MikhailBerezhanov/MAMboard/docs/Radiator_ABM-161-30_HS-117-30.pdf

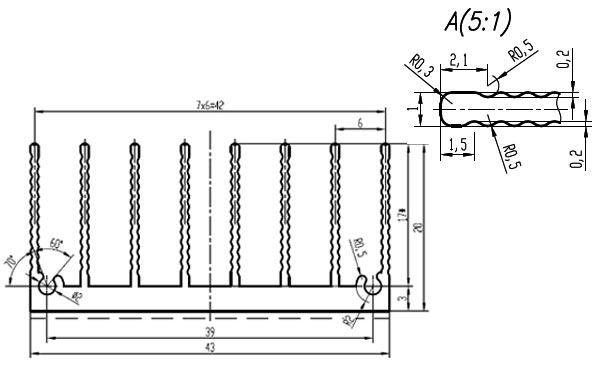
[picture p3: page 1]
