MikhailBerezhanov/MAMboard/docs/Battery_charger_TP4056_with_batt_protection_scheme.jpg

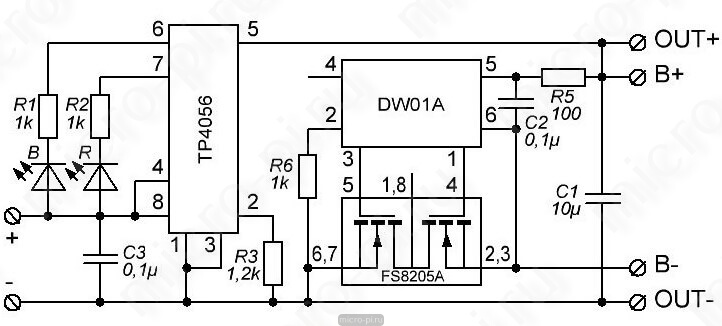
docs/Battery_charger_TP4056_with_batt_protection_scheme.jpg
