MikhailBerezhanov/MAMboard/docs/kak-podkluchit-regulator-gromkosti-k-usilitelu-resistor.jpg

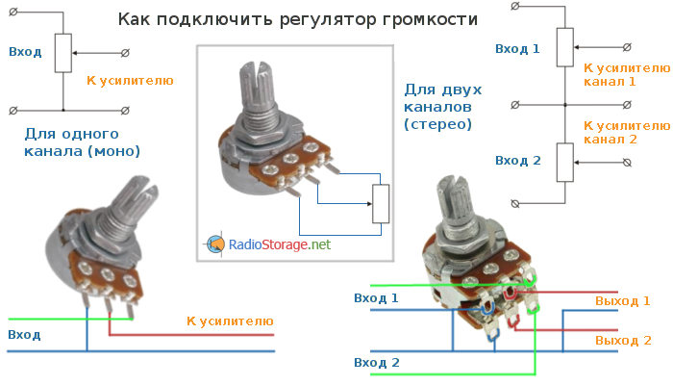
docs/kak-podkluchit-regulator-gromkosti-k-usilitelu-resistor.jpg
