MikhailBerezhanov/MAMboard/docs/LCD_I2C-PCF8574T-HAT.jpg

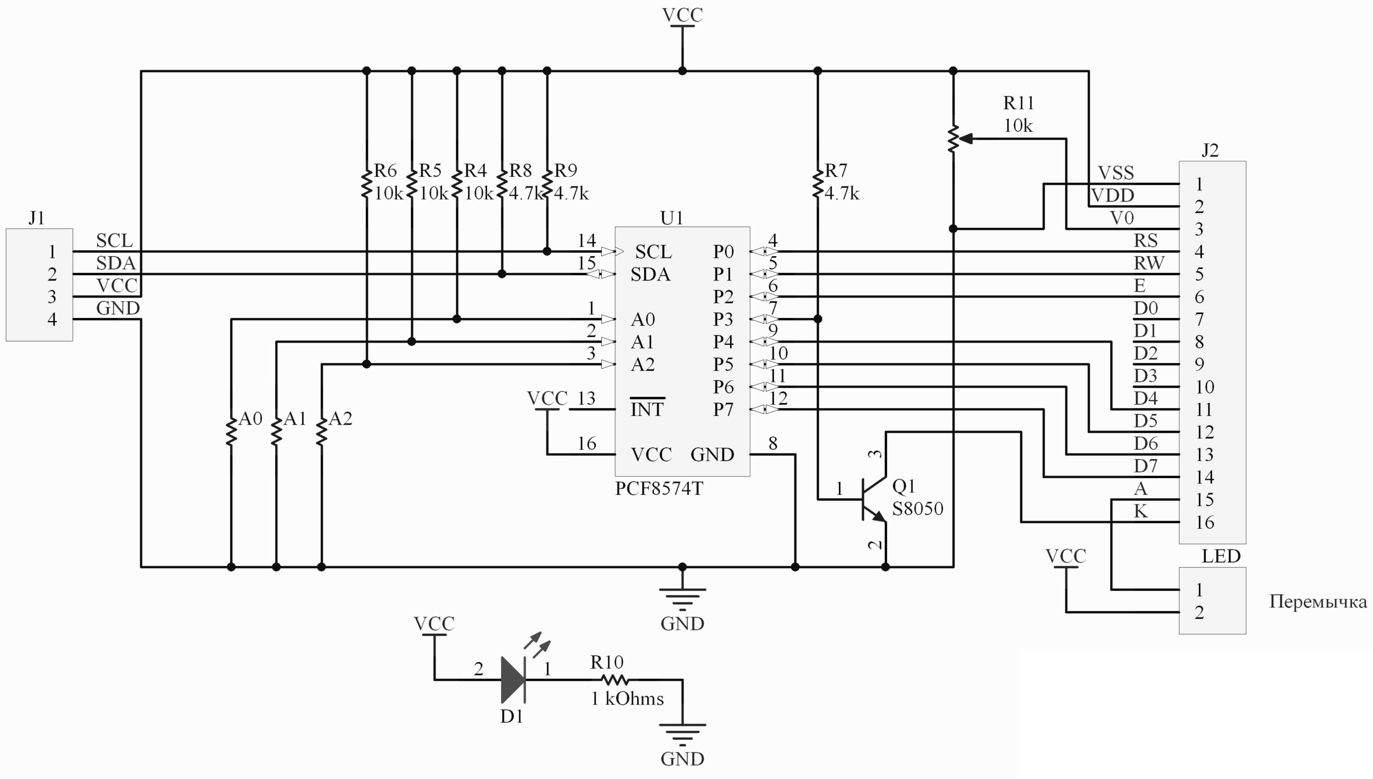
docs/LCD_I2C-PCF8574T-HAT.jpg
