MikhailBerezhanov/MAMboard/docs/midland_MA-26L.png

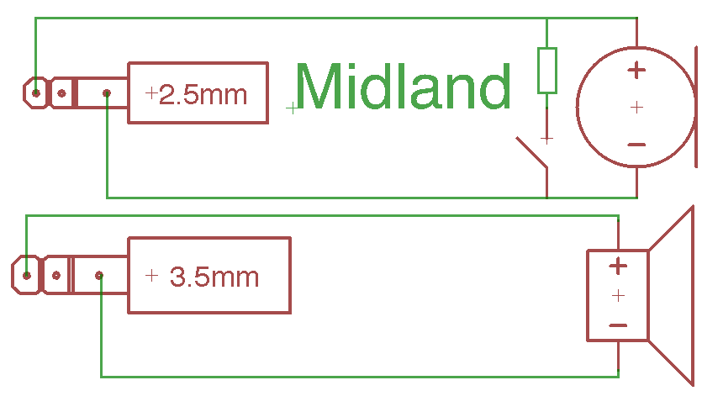
docs/midland_MA-26L.png
