MikhailBerezhanov/MAMboard/docs/NAU.jpg

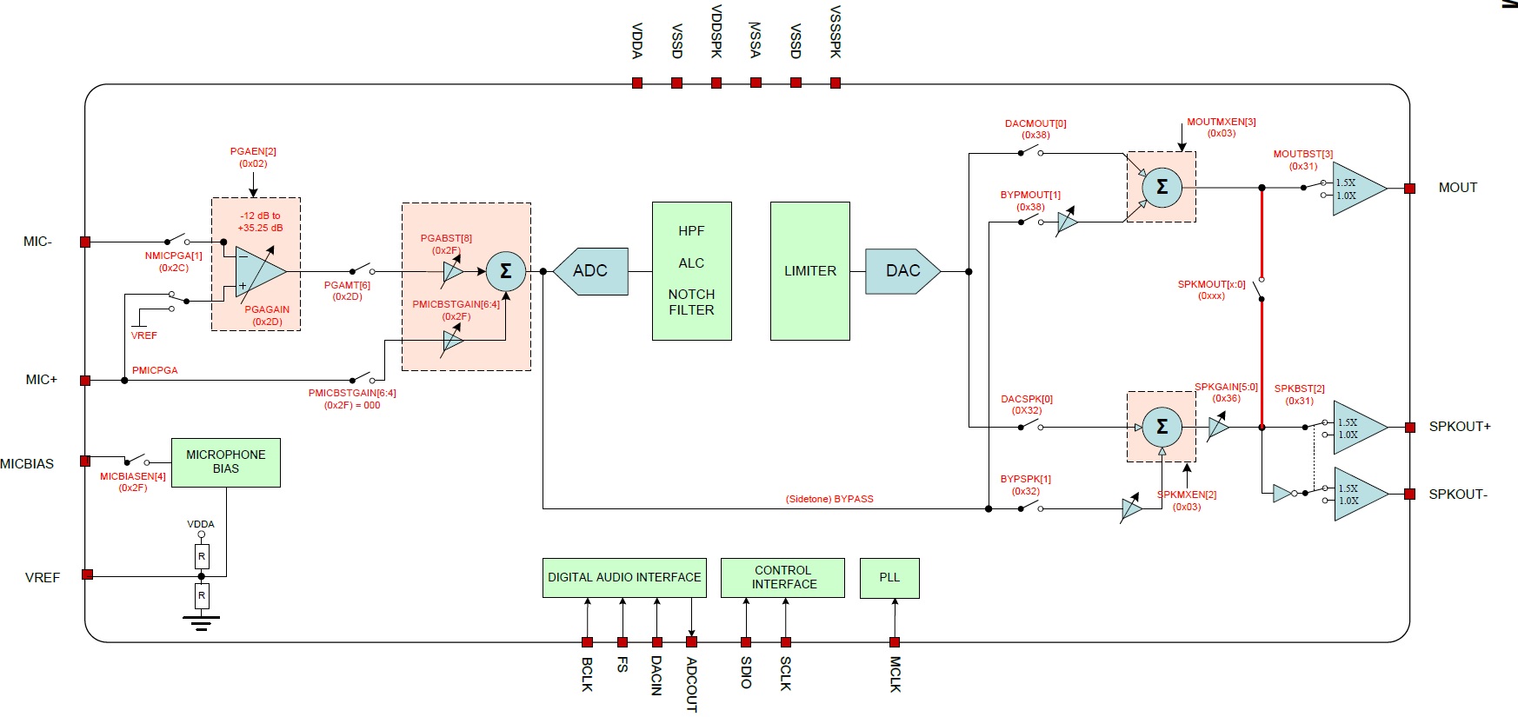
docs/NAU.jpg
