MikhailBerezhanov/MAMboard/docs/NAU_registers.jpg

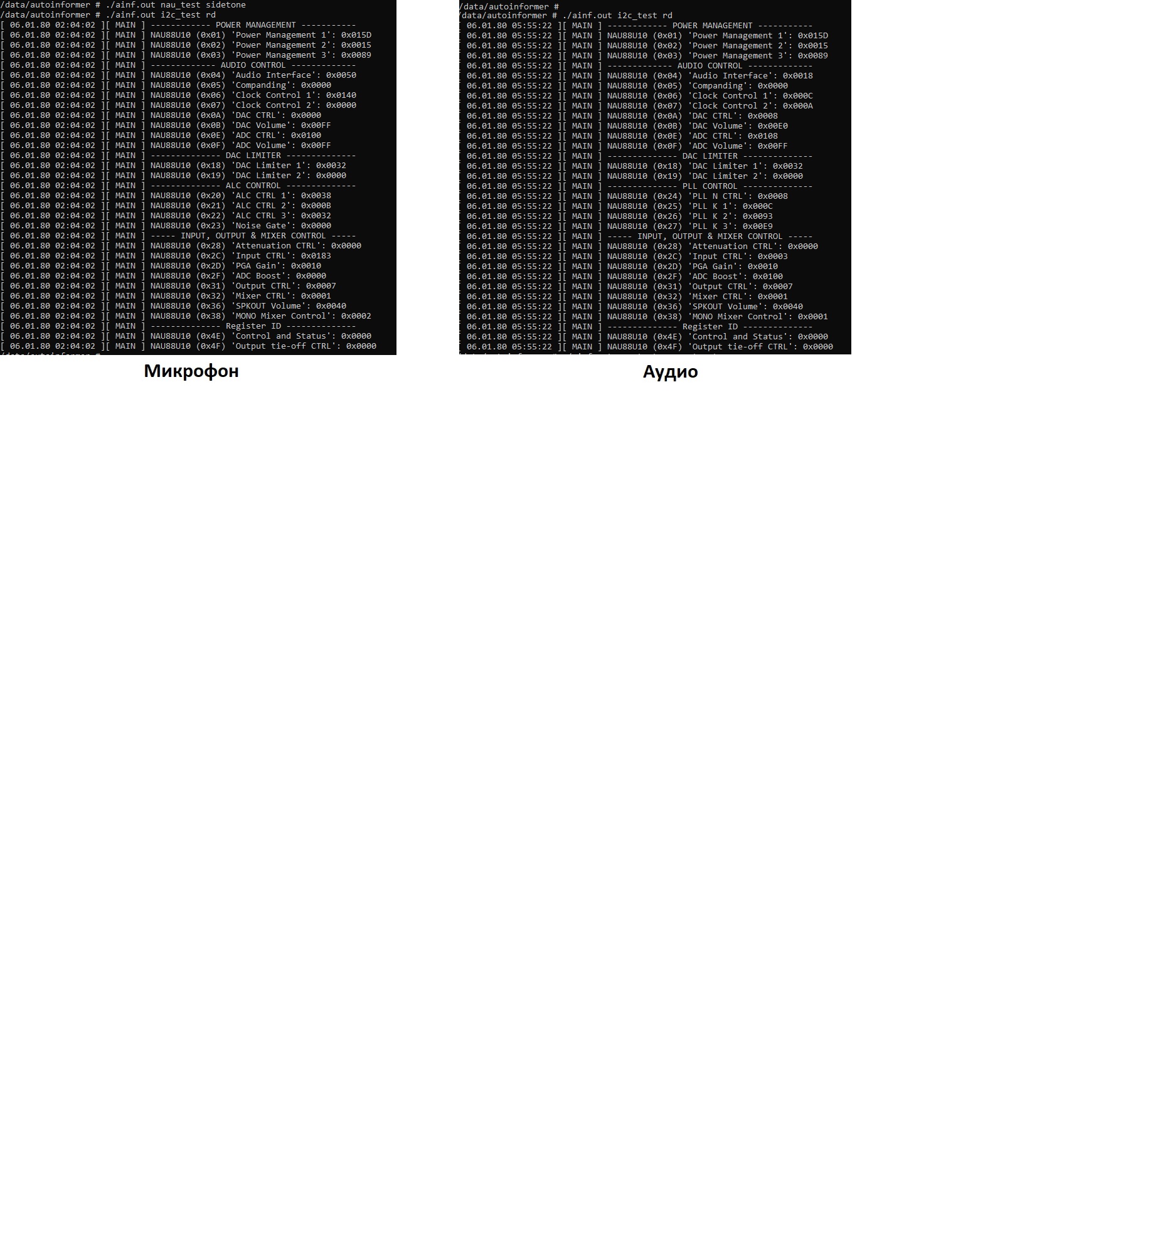
docs/NAU_registers.jpg
