MikhailBerezhanov/MAMboard/docs/oscilloscopes/LCD/PCA9306_I2C_with_10k_pullups.jpg

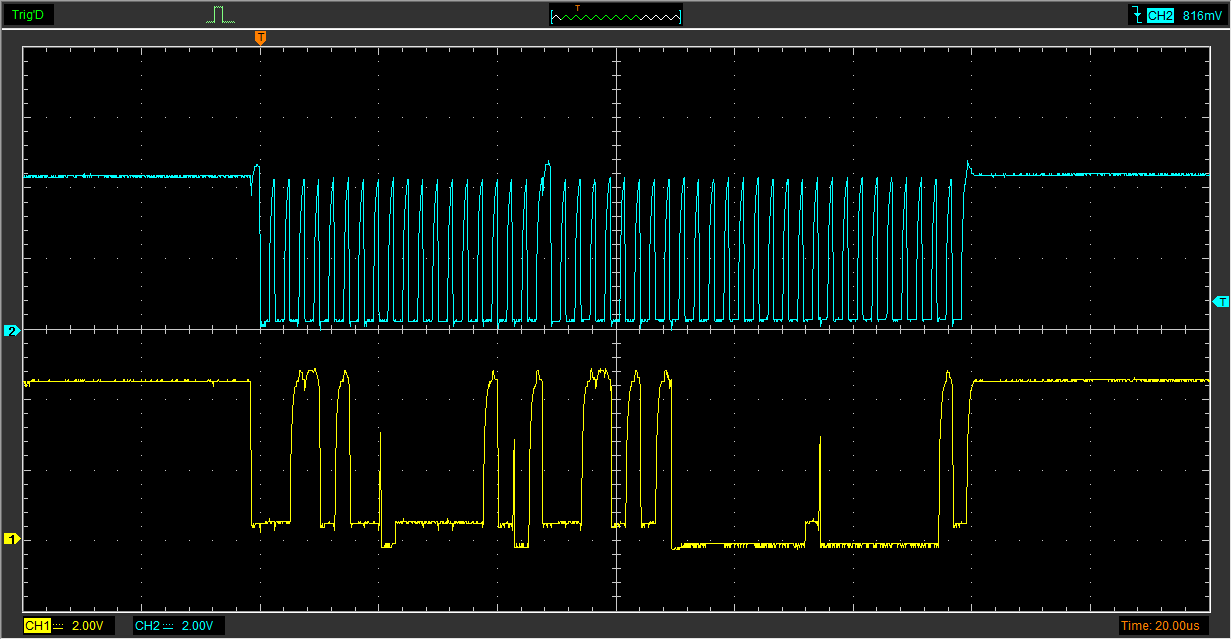
docs/oscilloscopes/LCD/PCA9306_I2C_with_10k_pullups.jpg
