MikhailBerezhanov/MAMboard/docs/oscilloscopes/LCD/stm32_100khz_7E.bmp

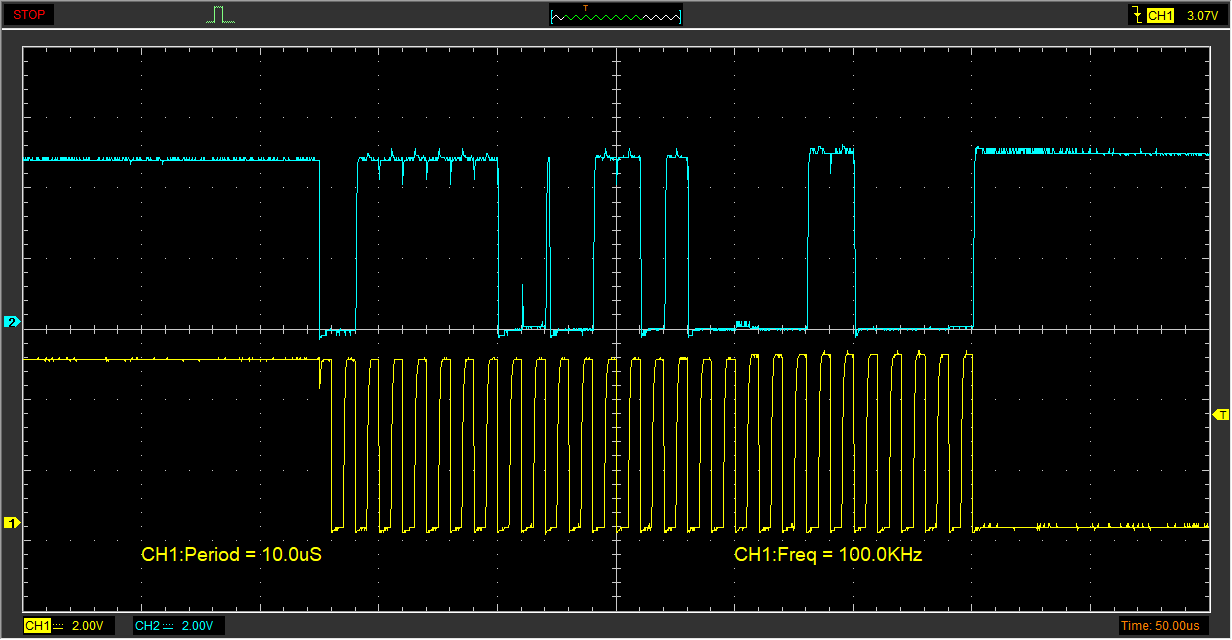
docs/oscilloscopes/LCD/stm32_100khz_7E.bmp
