MikhailBerezhanov/MAMboard/docs/oscilloscopes/NAU8810/PCM_CLK.jpg

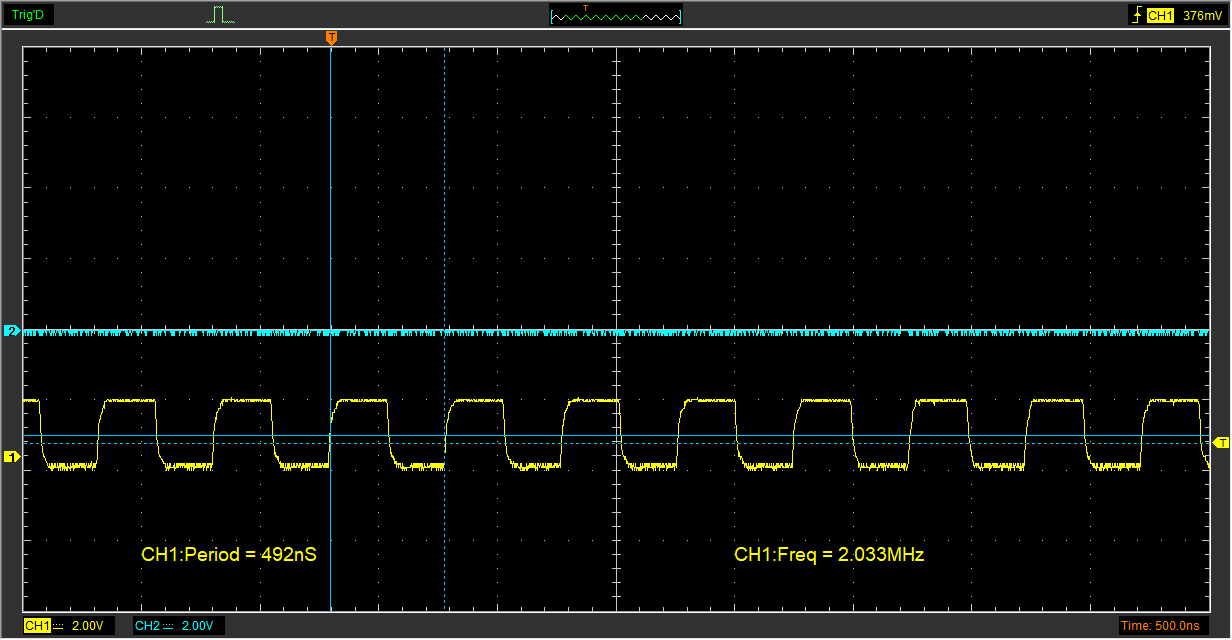
docs/oscilloscopes/NAU8810/PCM_CLK.jpg
