MikhailBerezhanov/MAMboard/docs/oscilloscopes/NAU8810/PCM_CLK_0.jpg

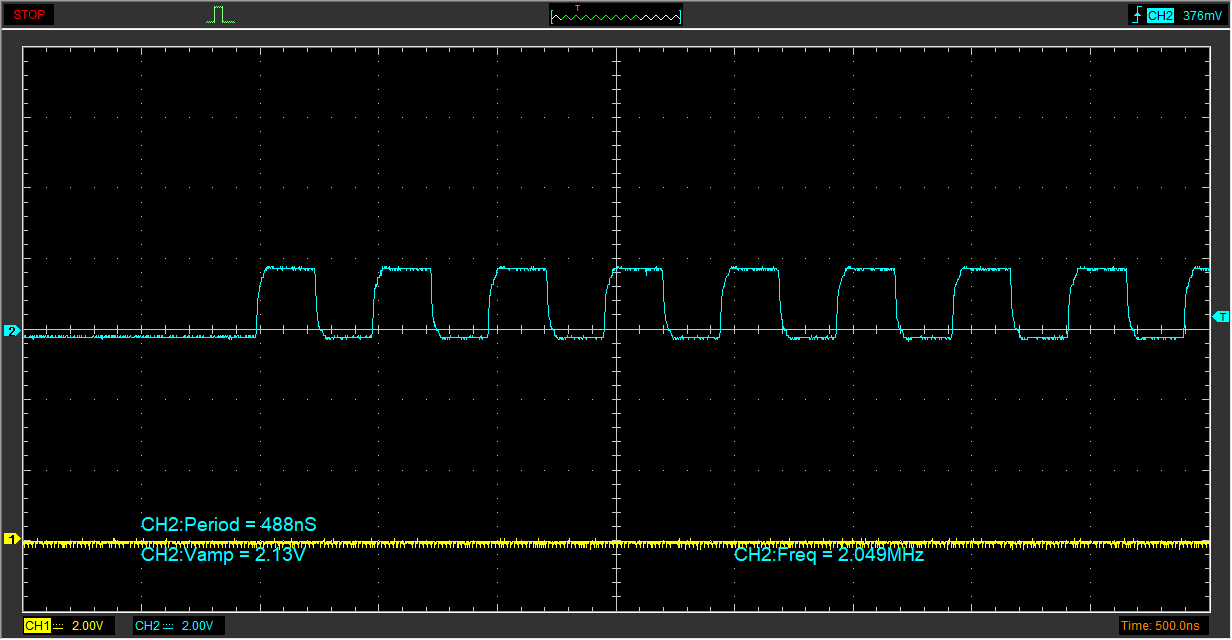
docs/oscilloscopes/NAU8810/PCM_CLK_0.jpg
