MikhailBerezhanov/MAMboard/docs/pcf_i2c_address.jpg

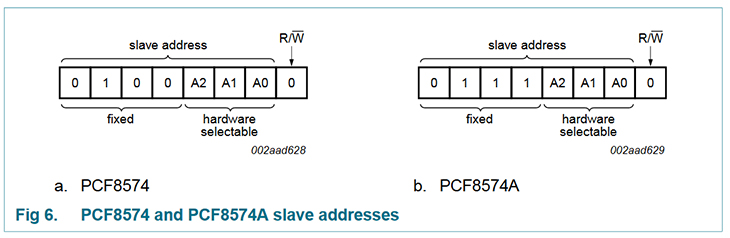
docs/pcf_i2c_address.jpg
