MikhailBerezhanov/MAMboard/docs/photo_2021-02-10_12-08-06.jpg

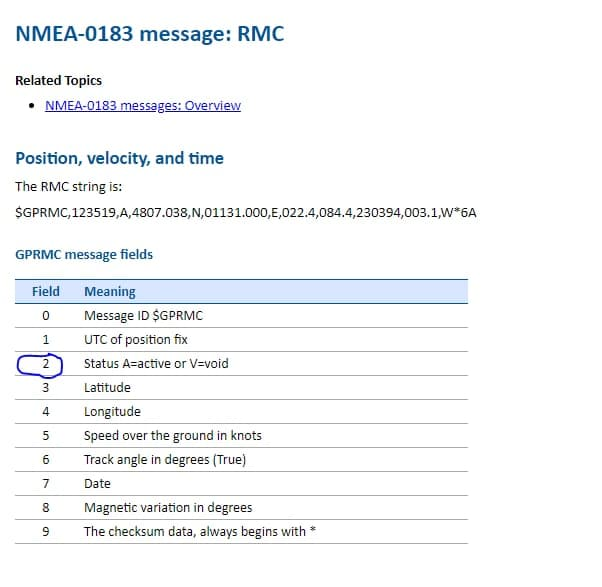
docs/photo_2021-02-10_12-08-06.jpg
