MikhailBerezhanov/MAMboard/docs/PJ-311D_connector.jpg

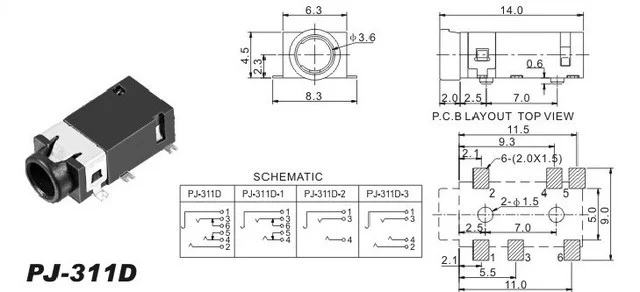
docs/PJ-311D_connector.jpg
