MikhailBerezhanov/MAMboard/docs/SIM7600-HEAD-CONNECTORS.jpg

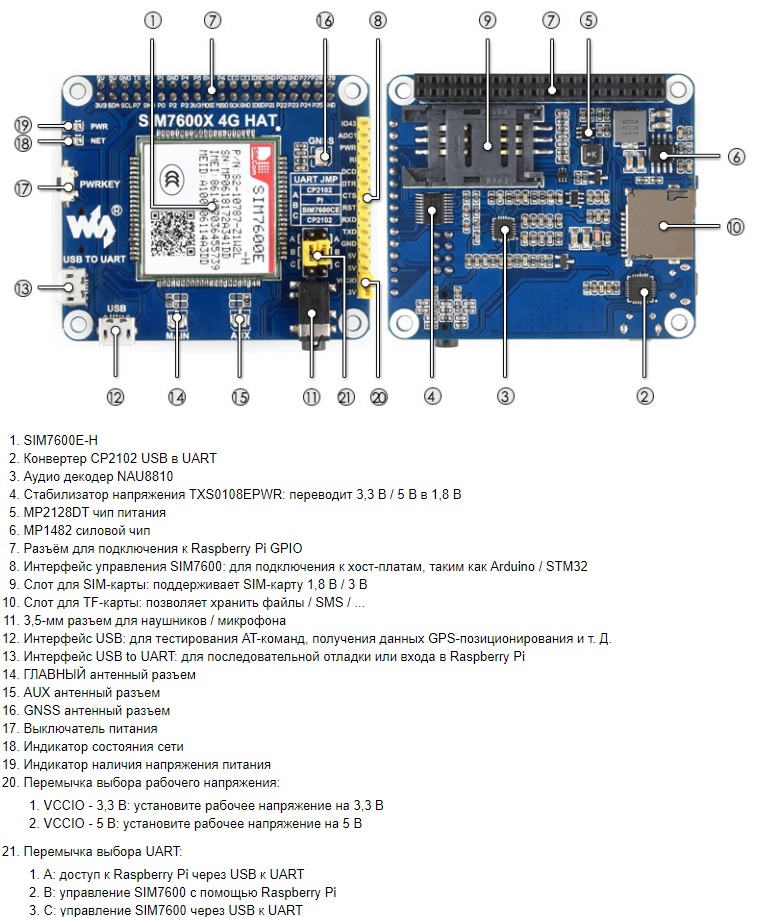
docs/SIM7600-HEAD-CONNECTORS.jpg
