MikhailBerezhanov/MAMboard/docs/usilitel-na-tda-2003-s-regulyatorom-gromkosti-2.gif

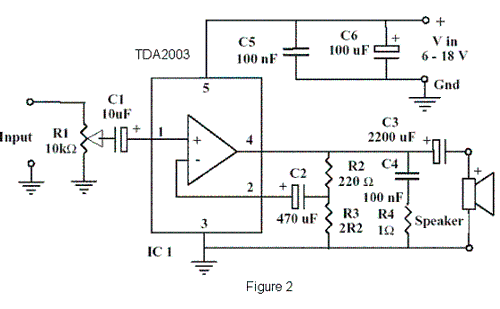
docs/usilitel-na-tda-2003-s-regulyatorom-gromkosti-2.gif
