MikhailBerezhanov/MAMboard/pcb/v1.1/GPIOs.jpg

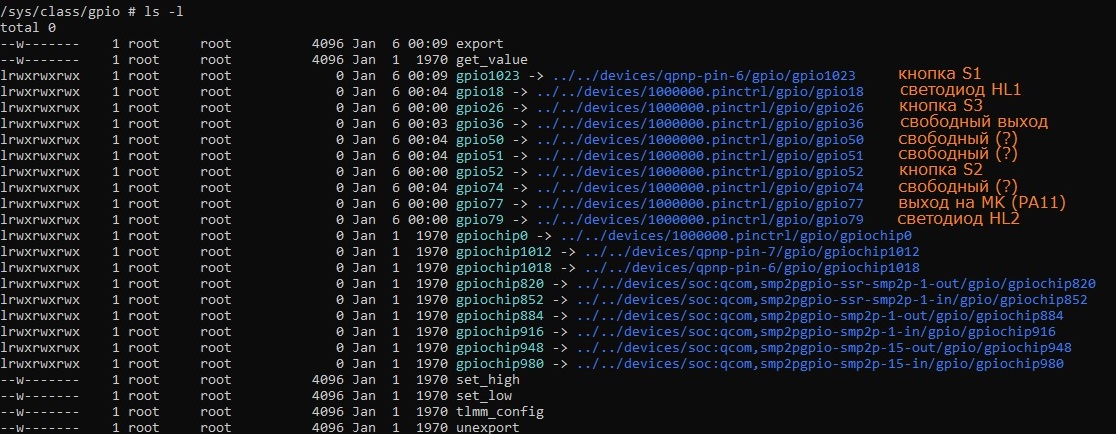
pcb/v1.1/GPIOs.jpg
