MikhailBerezhanov/MAMboard/pcb/v1.1/LCD_connector.jpg

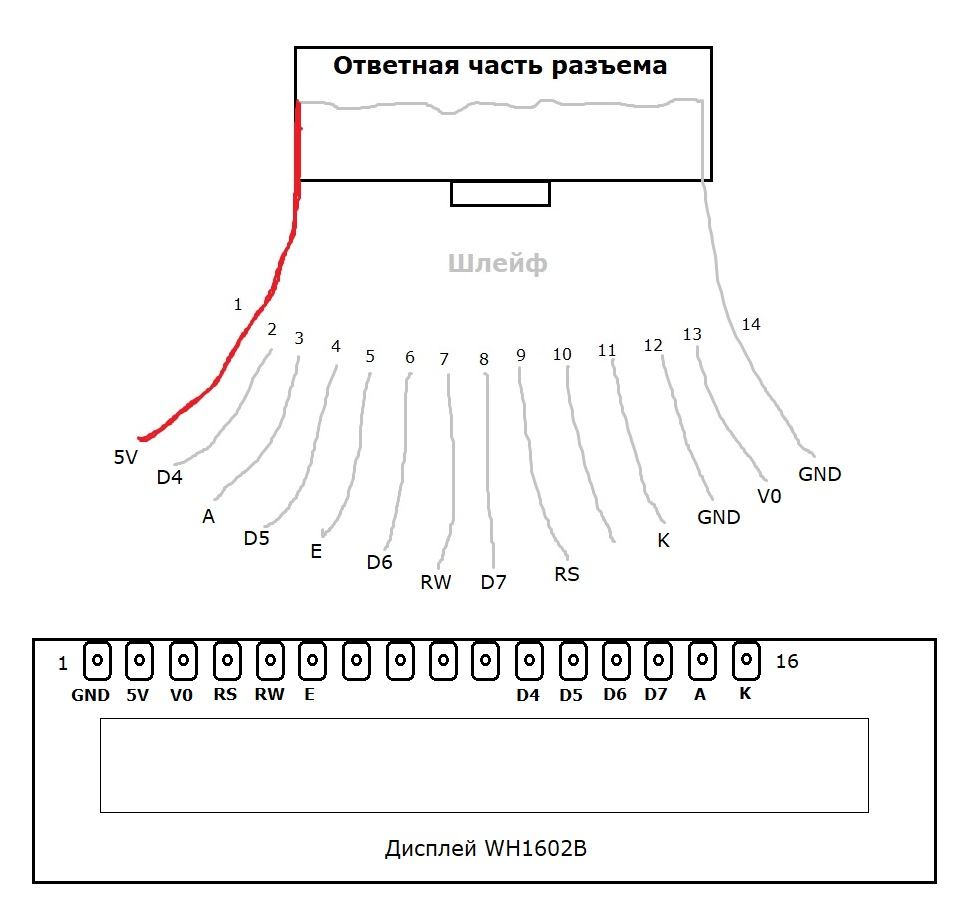
pcb/v1.1/LCD_connector.jpg
