MikhailBerezhanov/MAMboard/pcb/v1.1/Project Outputs for Autoinformer_v1.1/Autoinformer_v1.2pre_BOM.xls

Sheet: Autoinformer_v1.1
Конфигурация
 | Версия | Количество
 | v1.2pre | 15
Designator | Comment | Description | Quantity | Total | Link1URL | Link2URL | Link3URL | Link4URL | Link5URL | Link6URL | Link7URL
ANT1 | 146200-00011 | LTE Cellular Ceramic Antenna 698MHz-2.7GHz , SMT | 1 | 15 | https://www.elitan.ru/price/item17428368
C1, C11, C12, C13, C24, C28 | 4.7uF | GRM188R60J475KE19D | 6 | 90 | https://www.chipdip.ru/product/grm188r60j475ke19d | https://www.electronshik.ru/item/MUR/GRM188R60J475KE19D
C2, C3, C8, C14, C15, C16, C32, C34, C35, C40, C45, C46, C47, C48, C49, C52, C53, C54, C59, C61, C67, C68, C71, C76, C77, C79, C82 | 0.1uF | GRM188R71H104KA93D | 27 | 405 | https://www.chipdip.ru/product0/226236018 | https://www.electronshik.ru/item/MUR/GRM188R71H104KA93D |  |  | плюс 400
C4, C6, C17, C18, C29 | 10pF | GRM1885C1H100J | 5 | 75 | https://www.chipdip.ru/product/grm1885c1h100j | https://www.electronshik.ru/item/MUR/GRM1885C1H100JA01D
C5, C7, C9, C50, C51 | 22pF | GRM1885C1H220JA01D | 5 | 75 | https://www.chipdip.ru/product/grm1885c1h220j | https://www.electronshik.ru/item/MUR/GRM1885C1H220JA01D
C10 | 10nF | GRM188R71H103K | 1 | 15 | https://www.chipdip.ru/product0/9000143994 | https://www.electronshik.ru/item/MUR/GRM188R71H103KA01D
C19, C20, C44 | 33pF | GRM1885C1H330J | 3 | 45 | https://www.chipdip.ru/product0/565764982 | https://www.electronshik.ru/item/MUR/GRM1885C1H330JA01D
C21 | 100pF | GRM1885C1H101J | 1 | 15 | https://www.chipdip.ru/product0/305749128 | https://www.electronshik.ru/item/MUR/GRM1885C1H101JA01D
C22, C23, C25, C63 | 1uF | GRM188R71E105KA12D | 4 | 60 | https://www.chipdip.ru/product/grm188r71e105ka12d | https://www.electronshik.ru/item/MUR/GRM188R71E105KA12D
C26, C27 | 470uF 6.3V | 293D477X06R3E2TE3 Конденсатор танталовый SMD тип Е | 2 | 30 | https://www.chipdip.ru/product0/145634327?from=suggest_product
C30 | 1uF | GRM31MR71E105KA01L | 1 | 15 | https://www.chipdip.ru/product/grm31mr71e105k | https://www.electronshik.ru/item/MUR/GRM31MR71E105KA01L
C31 | 10uF 10V | Конденсатор танталовый SMD 10uF 10V тип B | 1 | 15 | https://www.chipdip.ru/product0/146061461?from=suggest_product
C33, C80, C81 | 0.1uF | CL05B104KO5NNNC (CC0402KRX7R7BB104) | 3 | 45 | https://www.chipdip.ru/product1/8001849671?from=suggest_product | https://www.electronshik.ru/item/SAMSUNG/CL05B104KO5NNNC
C36 | 0.039uF | CC0603KRX7R9BB393 | 1 | 15 | https://www.chipdip.ru/product0/8160066189?from=suggest_product | https://www.elitan.ru/price/item8778633 | https://www.electronshik.ru/item/YAG/CC0603KRX7R9BB393
C37 | K50-35 470uF 16V | Конденсатор электролитический алюминиевый 470мкФ, 16В, 8х12мм Р:3.5мм | 1 | 15 | https://www.chipdip.ru/product0/9000565914
C38, C39 | K50-35 1000uF 25V | Конденсатор электролитический алюминиевый 1000мкФ, 25В, 10x21мм | 2 | 30 | https://www.chipdip.ru/product0/9000565765?from=suggest_product
C41 | 22pF | GRM21A5C2E220J (CC0805JRNPO9BN220) | 1 | 15 | https://www.chipdip.ru/product0/29844 | https://www.electronshik.ru/item/MUR/GRM21A5C2E220JW01D
C42, C43 | NС | 0603 SMD Capacitor | 2 | 30
C55 | 100pF 2kV | C1206C101KGRACAUTO (CC1206JKNPODBN101) | 1 | 15 | https://www.elitan.ru/price/item16896874 | https://www.electronshik.ru/item/KEM/C1206C101KGRACAUTO
C56 | K50-35 220uF 50V | SH050M0220B5S-1012 ECAP 10*12 Конденсатор электролитический алюминиевый | 1 | 15 | https://www.chipdip.ru/product0/9000565903
C57, C64 | 10uF | GRM188R61E106M | 2 | 30 | https://www.chipdip.ru/product/grm188r61e106m | https://www.electronshik.ru/item/MUR/GRM188R61E106MA73D
C58 | K50-35 220uF 16V | ECA1CM221 6.3x11 P:2,5мм Конденсатор электролитический алюминиевый | 1 | 15 | https://www.chipdip.ru/product0/9000565899
C60, C69, C74, C75 |  | ECA0JHG221 5x11мм Р:2,5мм Конденсатор электролитический алюминиевый | 4 | 60 | https://www.chipdip.ru/product0/9000261774?from=suggest_product
C62 | K50-35 100uF 16V | SH016M0100A2F-0511 5x11мм Конденсатор электролитический алюминиевый | 1 | 15 | https://www.chipdip.ru/product0/9000565888
C65, C78 | K50-35 33uF 6.3V | Конденсатор электролитический алюминиевый 33 мкФ, 6.3 В, 4х7мм | 2 | 30 | https://www.chipdip.ru/product0/9000261769
C66 | 0.47uF | C1608X7R1H474K080AC (CC0603KRX7R9BB474) | 1 | 15 | https://www.chipdip.ru/product0/8576565346 | https://www.electronshik.ru/item/TDK/C1608X7R1H474K080AC
C70 | K50-35 680uF 25V | Конденсатор электролитический алюминиевый 680мкФ, 25В, 10х16мм Р:5мм | 1 | 15 | https://www.chipdip.ru/product0/9000565919
C72, C73 | K50-35 100uF 10V | SH010M0100B2F-0511 5x11мм Конденсатор электролитический алюминиевый | 2 | 30 | https://www.chipdip.ru/product0/46079?from=suggest_product | https://www.chipdip.ru/product0/9000565886
D1 | SIM7600E-H | Multi-Band LTE-TDD/LTE-FDD/HSPA+ and GSM/GPRS/EDGE module | 1 | 15 | http://www.mt-system.ru/SIMCom/SIM7600E-H |  |  |  | плюс 1
D2 | NAU8810YG | AUDIO CODEC MONO 20QFN | 1 | 15 | https://upverter.com/upn/revision/eec1ccdac07fe113/ | http://www.nuvoton.com/hq/resource-download.jsp?tp_GUID=DA00-NAU8810.1 | https://www.elitan.ru/price/index.php?find=NAU8810YG&delay=-1&mfg=all&seenform=y
D3 | TXB0102DCU | Voltage Level Translator Bidirectional 1 Circuit 2 Channel 100Mbps 8-VSSOP | 1 | 15 | https://www.elitan.ru/price/item692394 | https://www.chipdip.ru/product0/8002872138?from=suggest_product | https://www.electronshik.ru/item/TI/TXB0102DCUR
D4 | TXB0104PWR | 4-Bit Bidirectional Voltage-Level Shifter with Auto Direction Sensing and +/-15 kV ESD Protect 14-TSSOP -40 to 85 | 1 | 15 | https://www.elitan.ru/price/item703962
D5 | DW01A | НЕ УСТАНАВЛИВАТЬ | 1 | 15
D6 | MCP130T-450I/TT | 4.50 V 150 ms Microcontroller Supervisory Circuit - SOT-23-3 | 1 | 15 | https://www.elitan.ru/price/item505438 | https://www.electronshik.ru/item/MCRCH/MCP130T-450I%3A%3ATT
D7 | NB3N501DG | PLL Clock Multiplier Single 8-Pin SOIC 3 V ~ 5.25 V | 1 | 15 | https://www.elitan.ru/price/item9787428 | https://www.electronshik.ru/item/ONS/NB3N501DG
D8 | PCF8574AT | 8-bit I/O expander for I2C bus with interrupt PCF8574(A)T/3 - 100kHz version PCA8574(A)D - 400kHz version | 1 | 15 | https://www.elitan.ru/price/item981552 | https://www.electronshik.ru/item/NXP/PCF8574AT%3A%3A3.518
DA1 | TDA2003V | Amplifier IC 1-Channel _Mono_ Class AB 5-PENTAWATT 10W | 1 | 15 | https://www.elitan.ru/price/item123031 | https://www.chipdip.ru/product/tda2003v?from=suggest_product | https://www.chipdip.ru/product/hs-117-30
DA2 | LM2576S-5.0 | Импульсный понижающий регулятор напряжения, 5В, 3А, [TO-263] | 1 | 15 | https://www.chipdip.ru/product/lm2576sx-5.0-nopb | https://www.elitan.ru/price/item100181
DA3 | TP4056 | Li-lon Battery Charger 1A Standalone Linear with Thermal Regulation in SOP-8 | 1 | 15 | https://www.elitan.ru/price/item26170288 | https://www.electronshik.ru/item/YOUTAI/TP4056
DA4 | LM2577S-ADJ | Преобразователь постоянного тока повышающий 3 А вход 3.5...40В выход 5...60В -40...+125°С | 1 | 15 | https://www.elitan.ru/price/item100192 | https://www.electronshik.ru/item/TI/LM2577S-ADJ%3A%3ANOPB
DA5 | MIC29302WU | 3A Fast Response LDO Regulator Operating Input Voltage Range: 3V to 16V 1.24V to 15V Adjustable Output Voltage | 1 | 15 | https://www.elitan.ru/price/item637427 | https://www.chipdip.ru/product0/8000649332 | https://www.electronshik.ru/item/MCRCH/MIC29302WU
DA6 | LM1117GS-ADJ | LDO +1.25...13.8 В, 1А [SOT-223] Линейный регулятор с низким падением напряжения, Максимальное входное напряжение, 20 В | 1 | 15 | https://www.chipdip.ru/product/lm1117gs-adj | https://www.elitan.ru/price/item21580115
DA7 | LM1117GS-3.3 | LDO +3.3 В, 1А [SOT-223] Линейный регулятор с низким падением напряжения, Максимальное входное напряжение, 20 В | 1 | 15 | https://www.chipdip.ru/product/lm1117gs-3.3 | https://www.elitan.ru/price/item21580113
DD1 | STM32L151CBT6A | Analog - STM32L071C8T6 Микроконтроллер 32-Бит, Cortex-M3, 32МГц, 128КБ Flash, LCD, USB, ADC, DAC [LQFP-48] | 1 | 15 | https://www.elitan.ru/price/item11268663 | https://www.chipdip.ru/product/stm32l151cbt6a-2
F1 | MF-SM185/33-2 | Самовосстанавливающийся предохранитель PTC 1.8A(hold) 3.6A(trip) 33VDC 40A 1.9W 5s 0.04Ohm SMD 3425 Solder Pad 9.5 X 6.71 X 3mm | 1 | 15 | https://www.elitan.ru/price/item781521 | https://www.chipdip.ru/product0/8001787493?from=suggest_product
F2 | 1812L125/6PR | Предохранитель SMD 6 VDC 2.5 A | 1 | 15 | https://www.elitan.ru/price/item387111 | https://www.electronshik.ru/item/LTL/1812L125%3A%3A6PR
HL1 | TO-1608BC-MYF | Vf =2 V, 20mA, 0603 (HL-PST-1608S31YC) | 1 | 15 | https://www.chipdip.ru/product/to-1608bc-myf?from=suggest_product | https://www.chipdip.ru/product/gnl-3012ed
HL2 | TO-1608BC-MRE | Vf =2 V, 20mA, 0603 (HL-PST-1608S9AC) | 1 | 15 | https://www.chipdip.ru/product/to-1608bc-mre?from=suggest_product | https://www.elitan.ru/price/item16986056 | https://www.chipdip.ru/product/gnl-3012ed
HL3 | TO-1608BC-PG | Vf =3.3 V, 20mA, 0603 (HL-PST-1608U51GC) | 1 | 15 | https://www.chipdip.ru/product/to-1608bc-pg?from=suggest_product | https://www.elitan.ru/price/item16986058
HL4 | TO-1608BC-BF | Vf =3.3 V, 20mA, 0603 (HL-PST-1608H203BC) | 1 | 15 | https://www.chipdip.ru/product/to-1608bc-bf?from=suggest_product | https://www.elitan.ru/price/item16986057
IND1 | BLM21PG121SN1D | 0805, Дроссель подавления ЭМП 120Ohm 25% 100MHz 3A | 1 | 15 | https://www.chipdip.ru/product0/8228217893 | https://www.elitan.ru/price/item1364359
IND2, IND3, IND4, IND8, IND9 | BLM21SP102SN1D | 0805, Дроссель подавления ЭМП 1KOhm 25% 100MHz 1.6A 0.12Ohm | 5 | 75 | https://www.chipdip.ru/product/blm21sp102sn1d | https://www.elitan.ru/price/item21298136
IND5, IND7 | BLM21PG221SN1D | 0805, Дроссель подавления ЭМП 220Ohm +25% 100MHz 2A 45mOhm | 2 | 30 | https://www.chipdip.ru/product/blm21pg221sn1d | https://www.elitan.ru/price/item305175 |  |  | плюс 10
IND6 | BLM21PG300SN1D | 0805, Дроссель подавления ЭМП 100МГц:30Ом; 3А | 1 | 15 | https://www.chipdip.ru/product/blm21pg300sn1d | https://www.elitan.ru/price/item310735
L1 | LQG18HN47NJ | Чип индуктивность многослойная неэкранированная 47нГн 5% 100МГц Maximum DC Current 300 mA Maximum DC Resistance 700 mOhms | 1 | 15 | https://www.elitan.ru/price/item307313 | https://www.chipdip.ru/product/lqg18hn47nj?from=suggest_product
L2 | SRR1208-330YL | SMD индуктивность проволочная, на ферритовом сердечнике, экранированная 33uH 15% 1KHz 23Q-Factor Ferrite 2.8A 62mOhm | 1 | 15 | https://www.chipdip.ru/product/srr1208-330yl?from=suggest_product | https://www.elitan.ru/price/item319349
L3 | SRR1208-680YL | SMD индуктивность проволочная, на ферритовом сердечнике, экранированная 68uH 15% 1KHz 23Q-Factor Ferrite 2.8A 62mOhm | 1 | 15 | https://www.chipdip.ru/product1/8002012849?from=suggest_product | https://www.elitan.ru/price/item782382
LC1 | BNX003-01 | EMI фильтр индуктивно-емкостной 10A 150VDC 40дБ | 1 | 15 | https://www.elitan.ru/price/item279156 | https://www.chipdip.ru/product/bnx003-01?from=suggest_product
R1, R2, R9, R11, R13, R25, R78 | 0 | RC0603JR-070RL | 7 | 105 | https://www.chipdip.ru/product0/9000070541 | https://www.electronshik.ru/item/YAG/RC0603JR-070RL
R3, R73 | 68 | RC0603FR-0768RL | 2 | 30 | https://www.chipdip.ru/product0/9000079612 | https://www.electronshik.ru/item/YAG/RC0603FR-0768RL
R4, R5, R6, R27, R28, R31, R34, R35, R36, R38, R46, R47, R48, R49, R74, R75, R79, R80, R81, R82 | 10k | RC0603FR-0710KL (CRCW060310K0FKEA) | 20 | 300 | https://www.chipdip.ru/product0/9000079736 | https://www.electronshik.ru/item/VISHAY/CRCW060310K0FKEA
R8, R10, R12, R32 | 0 (NC) | НЕ УСТАНАВЛИВАТЬ | 4 | 60 | https://www.chipdip.ru/product0/9000070541 | https://www.electronshik.ru/item/YAG/RC0603JR-070RL
R14, R15, R16 | 22 | RC0603FR-0722RL (RC0603JR-0722RL) | 3 | 45 | https://www.chipdip.ru/product0/9000079564 | https://www.electronshik.ru/item/FENGHUA/0603%20-22%20%D0%9E%D0%BC%205%25%20RC0603JR-0722RL%20%5BRS-03K220JT%5D
R17, R20, R21, R26, R29, R39 | 2.2k | RC0603FR-072K2L | 6 | 90 | https://www.chipdip.ru/product0/9000079720 | https://www.electronshik.ru/item/YAG/RC0603FR-072K2L |  |  | плюс 30
R18, R19, R55, R64, R67 | 1k | RC0603FR-071KL | 5 | 75 | https://www.chipdip.ru/product0/9000079676 | https://www.electronshik.ru/item/YAG/RC0603FR-071KL
R22, R23, R24 | 0 (NC) | НЕ УСТАНАВЛИВАТЬ | 3 | 45 | https://www.chipdip.ru/product0/153356071 | https://www.electronshik.ru/item/YAG/RC0805JR-070RL
R30, R40 | 360 | RC0603FR-07360RL | 2 | 30 | https://www.chipdip.ru/product0/9000079629 | https://www.electronshik.ru/item/YAG/RC0603FR-07360RL
R33 | 22k | RC0603FR-0722KL | 1 | 15 | https://www.chipdip.ru/product0/9000079744 | https://www.electronshik.ru/item/YAG/RC0603FR-0722KL
R37 | 39 | RC0603FR-0739RL | 1 | 15 | https://www.chipdip.ru/product0/9000079606 | https://www.electronshik.ru/item/YAG/RC0603FR-0739RL
R41 | 43 | RC0603FR-0743RL | 1 | 15 | https://www.chipdip.ru/product0/9000079607 | https://www.electronshik.ru/item/YAG/RC0603FR-0743RL
R42 | 2.2 | RC0603FR-072R2L | 1 | 15 | https://www.chipdip.ru/product0/9000079549 | https://www.electronshik.ru/item/YAG/RC0603FR-072R2L
R43 | 1 | RC0603FR-071RL | 1 | 15 | https://www.chipdip.ru/product0/9000079509 | https://www.electronshik.ru/item/YAG/RC0603FR-071RL
R44, R68 | 0 | RC0805JR-070RL | 2 | 30 | https://www.chipdip.ru/product0/153356071 | https://www.electronshik.ru/item/YAG/RC0805JR-070RL
R45 | 10 | RC0603FR-0710RL | 1 | 15 | https://www.chipdip.ru/product0/9000079557 | https://www.electronshik.ru/item/YAG/RC0603FR-0710RL
R50 | 1M | RC1206JR-071ML | 1 | 15 | https://www.chipdip.ru/product0/690816980 | https://www.electronshik.ru/item/YAG/RC1206JR-071ML
R51 | 18k | RC0603FR-0718KL | 1 | 15 | https://www.chipdip.ru/product0/9000079742 | https://www.electronshik.ru/item/YAG/RC0603FR-0718KL
R52 | 3.9k | RC0603FR-073K9L | 1 | 15 | https://www.chipdip.ru/product0/9000079726?from=suggest_product | https://www.electronshik.ru/item/YAG/RC0603FR-073K9L
R53 | 2 | WSC45272R000FEA SMD чип резистор, с проволочной обмоткой, 4527, 2 Ом, Серия WSC, 2 Вт | 1 | 15 | https://www.chipdip.ru/product/wsc45272r000fea?from=suggest_product | https://www.elitan.ru/price/item572273
R54 | 1.2k | RC0603FR-071K2L | 1 | 15 | https://www.chipdip.ru/product0/9000079678 | https://www.electronshik.ru/item/YAG/RC0603FR-071K2L
R56 | 100 | RC0603FR-07100RL | 1 | 15 | https://www.chipdip.ru/product0/9000079616 | https://www.electronshik.ru/item/YAG/RC0603FR-07100RL
R57 | 16k | RC0603FR-0716KL | 1 | 15 | https://www.chipdip.ru/product0/9000079741 | https://www.electronshik.ru/item/YAG/RC0603FR-0716KL
R58 | 1.5k | RC0603FR-071K5L | 1 | 15 | https://www.chipdip.ru/product0/9000079716?from=suggest_product | https://www.electronshik.ru/item/YAG/RC0603FR-071K5L
R59, R63 | 100k | RC0603FR-07100KL | 2 | 30 | https://www.chipdip.ru/product0/9000079760 | https://www.electronshik.ru/item/YAG/RC0603FR-07100KL |  |  | плюс 30
R60 | 47k | RC0603FR-0747KL | 1 | 15 | https://www.chipdip.ru/product0/9000079752 | https://www.electronshik.ru/item/YAG/RC0603FR-0747KL
R61 | 470 | RC0805FR-07470RL | 1 | 15 | https://www.chipdip.ru/product0/9000079478 | https://www.electronshik.ru/item/YAG/RC0805FR-07470RL
R62 | 10k | RC0603FR-0710KL (CRCW060310K0FKEA) | 1 | 15 | https://www.electronshik.ru/item/VISHAY/CRCW060310K0FKEA | https://www.chipdip.ru/product0/9000079736 |  |  | плюс 100
R65 | 1.3k | RC0603FR-071K3L | 1 | 15 | https://www.chipdip.ru/product0/9000079679 | https://www.electronshik.ru/item/YAG/RC0603FR-071K3L
R66 | 0.1 | RL0805FR-070R1L | 1 | 15 | https://www.elitan.ru/price/item503786 | https://www.electronshik.ru/item/YAG/RL0805FR-070R1L
R69 | 3.3k | RC0603FR-073K3L | 1 | 15 | https://www.chipdip.ru/product0/9000079724 | https://www.electronshik.ru/item/YAG/RC0603FR-073K3L
R70 | 7.5k | RC0603FR-077K5L | 1 | 15 | https://www.chipdip.ru/product0/9000079733 | https://www.electronshik.ru/item/YAG/RC0603FR-077K5L
R71 | 1k | RC0402FR-071KL | 1 | 15 | https://www.chipdip.ru/product0/9000189652?from=suggest_product | https://www.electronshik.ru/item/YAG/RC0402FR-071KL
R72 | 1k | RC1206FR-071KL | 1 | 15 | https://www.chipdip.ru/product0/9000079635 | https://www.electronshik.ru/item/YAG/RC1206FR-071KL
R76, R84, R54new | 2k | RC0603FR-072KL | 3 | 45 | https://www.chipdip.ru/product0/9000079719 | https://www.electronshik.ru/item/YAG/RC0603FR-072KL |  |  | плюс 20
R77 | 120 | НЕ УСТАНАВЛИВАТЬ | 1 | 15 | https://www.chipdip.ru/product0/9000079464 | https://www.electronshik.ru/item/YAG/RC0805FR-07120RL
R83 | 5.6k | RC0603FR-075K6L | 1 | 15 | https://www.chipdip.ru/product1/8001784532 | https://www.electronshik.ru/item/YAG/RC0603FR-075K6L
S1, S2, S3, S5 | KLS7-TS6606 | 6x6 Tact Switch Series | 4 | 60 | https://www.chipdip.ru/product/kls7-ts6606-7.0-180-tc-0206 | https://www.elitan.ru/price/item22675038
S4 | 1437566-3 | SMD button | 1 | 15 | https://www.chipdip.ru/product/tyco-1437566-3-fsmsm?from=suggest_product | https://www.elitan.ru/price/item565583
VD1 | SMF05C | 12.5V Clamp 8A _8/20µs_ Ipp Tvs Diode Surface Mount SC-88/SC70-6/SOT-363 | 1 | 15 | https://www.elitan.ru/price/item10155001 | https://www.chipdip.ru/product/smf05ct1g?from=suggest_product
VD2, VD3, VD4 | ESD9L5.0ST5G | TVS диод защитный 5В_пиковое_рабочее 9.8В_ограничение SOD923 | 3 | 45 | https://www.elitan.ru/price/index.php?find=ESD9L5.0ST5G&delay=-1&mfg=all&seenform=y | https://www.chipdip.ru/product0/8001926257
VD5, VD18 | ESDA6V1SC5 | Сборка защитная TVS-диодов 5.25В_пиковое_ SOT23-5 Unidirectional Channels 4 Voltage - Reverse Standoff (Typ) 5.25V Voltage - Breakdown (Min) 6.1V | 2 | 30 | https://www.elitan.ru/price/item317230 | https://www.electronshik.ru/item/ST/ESDA6V1SC5 | https://www.chipdip.ru/product0/8001797118?from=suggest_product
VD6 | SP0503BAHTG | TVS Diode-3 Рабочее напряжение 5.5 В Максимальное напряжение фиксации 8.5 в | 1 | 15 | https://www.chipdip.ru/product/sp0503bahtg | https://www.elitan.ru/price/item393293
VD7 | MMSZ5231B-TP | Стабилитрон 5.1В, 5%, 0.5Вт, [SOD-123] | 1 | 15 | https://www.chipdip.ru/product/mmsz5231b-tp?from=suggest_product | https://www.elitan.ru/price/item685173
VD8, VD9, VD17 | ESD9L3.3ST5G | TVS диод защитный 5В_пиковое_рабочее 9.8В_ограничение SOD923 | 3 | 45 | https://www.elitan.ru/price/item1205491 | https://www.chipdip.ru/product1/8002974897?from=suggest_product
VD10 | LXES15AAA1-153 | TVS диоды Подавители ЭСР / диоды для подавления переходных скачков напряжения ESD Protection Device | 1 | 15 | https://www.chipdip.ru/product0/8001818635?from=suggest_product | https://www.elitan.ru/price/item11962267
VD11, VD16 | SS36 | Schottky; DO-214AB; 3.0A IF; 0.75V; 60V; 100A IFRM; 10000V/us; 1000pF | 2 | 30 | https://www.elitan.ru/price/item499214 | https://www.chipdip.ru/product/ss36-e3-57t-2?from=suggest_product
VD12 | SS510 | Диод Шоттки 5A 100V (SMC) | 1 | 15 | https://www.chipdip.ru/product0/8002382677?from=suggest_product | https://www.elitan.ru/price/item24826922
VD13 | SM15T39CA | TVS Diode Bi-Directional SM15T39CA 69.7V, 1500W, SMC 2-Pin | 1 | 15 | https://www.chipdip.ru/product/sm15t39ca?from=suggest_product | https://www.elitan.ru/price/item636974
VD14 | BAT60AE6327HTSA1 | Диод Шоттки 3А 10В [SOD-323] | 1 | 15 | https://www.chipdip.ru/product/bat60a?from=suggest_product | https://www.elitan.ru/price/item9533309
VD15 | SS34 | Schottky; DO-214AB; 3.0A IF; 0.75V; 40V; 100A IFRM; 10000V/us; 1000pF | 1 | 15 | https://www.chipdip.ru/product/ss34-5 | https://www.elitan.ru/price/item9505516
VT1 | 2N7002 | N-Channel MOSFET 60В 0.115А [SOT-23] | 1 | 15 | https://www.chipdip.ru/product/2n7002-tp-reel-3000 | https://www.elitan.ru/price/item484309
VT2, VT3 | BC850B | Transistor, Npn, 0.1A, 50V, Vbe = 0.7V, hfe = 240 [ SOT23 ] | 2 | 30 | https://www.chipdip.ru/product/bc850b?from=suggest_product | https://www.elitan.ru/price/item5642305
VT4 | FS8205A | НЕ УСТАНАВЛИВАТЬ | 1 | 15
VT6, VT7 | IRLML6402 | P-Channel 20V 3.7A _Ta_ 1.3W _Ta_ Surface Mount/SOT-23 | 2 | 30 | https://www.chipdip.ru/product/irlml6402tr?from=suggest_product | https://www.elitan.ru/price/item13518502
VT5, VT8, VT9, VT10 | BSS138 | MOSFET, N-канал, 0.2А, 50В, [SOT-23] | 4 | 60 | https://www.chipdip.ru/product/bss138-7-f-diodes?from=suggest_product | https://www.elitan.ru/price/item305174
VT11 | SI2308BDS-T1-GE3 | MOSFET, N-канал 60В 1.9А [SOT-23] | 1 | 15 | https://www.chipdip.ru/product/si2308bds-t1-ge3-vishay | https://www.electronshik.ru/item/VISHAY/SI2308BDS-T1-GE3 | https://www.elitan.ru/price/item668096
X1 | 5039600696 | Соединители для карт памяти 1mm microSIM Push Push SMT | 1 | 15 | https://www.elitan.ru/price/item12310026
X2 | 112J-TDAR-R | Разъем: для карт памяти; SD Micro; push-push; SMT; позолота | 1 | 15 | https://www.chipdip.ru/product0/8002703228 | https://www.elitan.ru/price/item10898530
X3 | 1050170001 | USB - micro B USB 2.0 Receptacle Connector 5 Position Surface Mount, Right Angle; Through Hole | 1 | 15 | https://www.elitan.ru/price/item5116026 | https://www.chipdip.ru/product/105017-0001-molex?position_type={position_type}|k50id|pla-293946777986|cid|11945324864|aid|488785225626|gid|115765259517&utm_campaign=G_tovarnieobjavlenija&utm_content=text1_ga&utm_term=
X4 | PY-401N | Гнездо моно 2.5мм | 1 | 15 | https://www.elitan.ru/price/index.php?find=PY-401N&delay=-1&mfg=all&seenform=y | https://www.chipdip.ru/product/py-401n
X5 | PY-601N | Аудио гнездо (М) 3.5мм | 1 | 15 | https://www.chipdip.ru/product/py-601n?from=suggest_product | https://www.elitan.ru/price/index.php?find=PY-601N&delay=-1&mfg=all&seenform=y
X6, X13 | DS1021_1x2 | Вилка штыревая 2.54мм 1x2 прямая PLS-2 | 2 | 30 | https://www.chipdip.ru/product/pls-2 | https://www.elitan.ru/price/item10669650
X7 | DS1013-14M | Вилка на плату прямая 14 конт. 2.54мм ответная часть: DS1016-14MA2BB или IDC-14F шлейф DS1057-14A282R-30.5 | 1 | 15 | https://www.elitan.ru/price/item21920938 | https://www.electronshik.ru/item/CONNFLY/DS1013-14MSIXA-B | https://www.chipdip.ru/product0/8160149550
X8, X15 | 2EDGR-5.08-02P | Клеммник разъемный угловой 2 конт., шаг 5.08 мм (KLS2-EDR-5.08-02P-4) 2EDGK-5.08-02P - ответная часть | 2 | 30 | https://www.chipdip.ru/product/kls2-edr-5.08-02p-4-2edgr-5.08-02p | https://www.elitan.ru/price/item21239767
X9 | U_FL-R-SMT-1_10 | Разъем РЧ / 50 Ом Коаксиальный, UFL Коаксиальный, Прямое Гнездо, Вертикальный Поверхностный Монтаж SMT | 1 | 15 | https://www.elitan.ru/price/item1203541 | https://www.chipdip.ru/product0/9000586248?from=suggest_product
X10 | KLS1-SMA002-B | Разъем угловой SMA гнездо на плату 50 Ом | 1 | 15 | https://www.platan.ru/cgi-bin/qwery.pl/id=356964102 | https://www.elitan.ru/price/item9893558
X11 | DS1021-2*3SF11-B | Вилка штыревая 2.54мм 2x3 прямая тип1 | 1 | 15 | https://www.chipdip.ru/product/pld-6 | https://www.electronshik.ru/item/CONNFLY/DS1021-2x3SF11-B
X12 | DS1021_2x8 | Вилка штыревая 2.54мм 2х8 прямая PLD-16 | 1 | 15 | https://www.chipdip.ru/product/pld-16 | https://www.elitan.ru/price/item14835380
X14 | Keystone 1029 | 16340 2/3A Battery Holder | 1 | 15 | https://www.elitan.ru/price/item468733
Y1 | HC49SM-8MHz | 8 MHz resonator | 1 | 15 | https://www.chipdip.ru/product/8mhz-hc-49sm | https://www.elitan.ru/price/item2093968
 | 16340 EagTac 750mAh 4,5А защищенный | Аккумулятор 16340 EAGTAC 750mAh защищенный | 1 | 15 | https://magzaryada.ru/akkumulyatory/14500-16340/eagletac-16340-rcr123 | https://www.lacrosse-nn.ru/%D0%B0%D0%BA%D0%BA%D1%83%D0%BC%D1%83%D0%BB%D1%8F%D1%82%D0%BE%D1%80%D1%8B-li-ion-14500-16340-rcr123/eagtac-16340-750mah-4-5a/
 | HS 117-30 | Радиатор 30х43х20 мм, 7.1 дюйм*градус/Вт | 1 | 15 | https://www.chipdip.ru/product/hs-117-30 | https://www.electronshik.ru/item/KLS/HS117-30
 | WH1602B-YYK-CTK | LCD Cyrillic дисплей 16X2 | 1 | 15 | https://www.electronshik.ru/item/WINSTAR/WH1602B-YYK-CTK%23
 | Крепеж радиатора к плате | Винт М2х6 круг , пл, шлиц - | 2 | 30 |  | https://www.sovelektron.com/vint-pf2-6/ | https://mirekom.ru/price/product-5410.11 | https://mirekom.ru/price/product-4708.10 | плюс 60
 | 2EDGK-5.08-02P-14 | Разъемный клеммный блок, ответная часть 2 контакта. Серия 2EDGK-5.08 | 2 | 30 | https://mirekom.ru/price/product-6612.20 | https://www.elitan.ru/price/item130957 | https://www.chipdip.ru/product/kls2-edk-5.08-02p-4s-2esdv-02p?from=suggest_product
 | IDC-14F (DS1016-14MA2BB) | Розетка кабельная с 14-контактами 2.54мм | 1 | 15 | https://www.elitan.ru/price/item8570145 | https://www.electronshik.ru/item/CONNFLY/DS1016-14MA2BB
 | DS1057-14A282R-30.5 | Плоский шлейф 14 жил 1.27мм | 1 | 15 | https://www.electronshik.ru/item/CONNFLY/DS1057-14A282R-30.5 | https://www.chipdip.ru/product/ds1057-14-30
 | GD900 30g | Термопаста | 1шт. На весь проект |  | https://tgt-store.ru/272186/ | https://aliexpress.ru/item/33047821777.html
 | Крепеж микросхемы к радиатору | Винт М3х8, круг , пл, шлиц - | 1 | 15 |  |  |  |  | плюс 20
Новая цепь питания аудио-усилителя (14.4 В)
DA4 | LM2596R-ADJ | Понижающий DC-DC преобразователь, Uвх=до 40В, Uвых=1.23…37, 3А, 150кГц [TO-263-5L] | 1 | 15 | https://www.chipdip.ru/product/lm2596r-adj |  |  |  | плюс 15
R57 | 0603 11k 1% | RC0603FR-0711KL | 1 | 15 |  |  |  |  | плюс 15
R58 | 0603 1k 1% | RC0603FR-071KL | 1 | 15 |  |  |  |  | плюс 15
 |  |  | 1 | 15
 |  |  | 1 | 15
 |  |  | 1 | 15
Основная цепь питания |  |  | 1 | 15
С58 | ECAP (К50-35), 1000мкФ, 10В | 8x11,5мм P:3.5мм, Конденсатор электролитический алюминиевый | 1 | 15 | https://www.chipdip.ru/product0/9000565921?from=suggest_product |  |  |  | плюс 20
 |  |  | 1 | 15
 |  |  | 1 | 15
 |  |  | 1 | 15
 |  |  | 1 | 15
R37 | 0805 39 1% | RC0805FR-0739RL | 1 | 15 |  |  |  |  | плюс 20
R41 | 0805 43 1% | RC0805FR-0743RL | 1 | 15 |  |  |  |  | плюс 20
R42 | 0805 2.2 1% | RC0805FR-072R2L | 1 | 15 |  |  |  |  | плюс 20
R43 | 0805 1 1% | RC0805FR-071RL | 1 | 15 |  |  |  |  | плюс 20
Rnew1 | 1210, 10 , 0.5 Вт | RC1210JR-0710RL | 1 | 15 |  |  |  |  | плюс 20
Rnew1 | 1210, 10 1%, 0.75 Вт | CRGP1210F10R | 1 | 15 |  |  |  |  | плюс 20
Rnew2 | 0612, 0.01 , 1 Вт | CFG0612-FX-R010ELF | 3 | 45 | https://www.elitan.ru/price/item20976639 |  |  |  | плюс50
 |  |  | 1 | 15
 |  |  | 1 | 15

Sheet: Закупка
Позиция | Комментарий | Наименование | Кол-во | Link1URL | Link2URL | Link3URL | Link4URL | Link5URL
C2, C3, C8, C14, C15, C16, C32, C34, C35, C40, C45, C46, C47, C48, C49, C52, C53, C54, C59, C61, C67, C68, C71, C76, C77, C79, C82 | 0.1uF | GRM188R71H104KA93D | 400 | https://www.chipdip.ru/product0/226236018 | https://www.electronshik.ru/item/MUR/GRM188R71H104KA93D
D1 | Multi-Band LTE-TDD/LTE-FDD/HSPA+ and GSM/GPRS/EDGE module | SIM7600E-H | 1 | http://www.mt-system.ru/SIMCom/SIM7600E-H
IND5, IND7 | 0805, Дроссель подавления ЭМП 220Ohm +25% 100MHz 2A 45mOhm | BLM21PG221SN1D | 20 | https://www.chipdip.ru/product/blm21pg221sn1d | https://www.elitan.ru/price/item305175
R17, R20, R21, R26, R29, R39 | 2.2k | RC0603FR-072K2L | 30
R59, R63 | 100k | RC0603FR-07100KL | 30
R62 | 10k | RC0603FR-0710KL (CRCW060310K0FKEA) | 100
R76, R84, R54new | 2k | RC0603FR-072KL | 20
R57 | 0603 11k 1% | RC0603FR-0711KL | 20
R58 | 0603 1k 1% | RC0603FR-071KL | 20
R37 | 0805 39 1% | RC0805FR-0739RL | 20
R41 | 0805 43 1% | RC0805FR-0743RL | 20
R42 | 0805 2.2 1% | RC0805FR-072R2L | 20
R43 | 0805 1 1% | RC0805FR-071RL | 20
Rnew1 | 1210, 10 , 0.5 Вт | RC1210JR-0710RL | 20
Rnew1 | 1210, 10 1%, 0.75 Вт | CRGP1210F10R | 20
Rnew2 | 2512, 0.015R, 5%, 1 Вт | RL2512JK-070R015L
Rnew2 | 0612, 0.01 , 1 Вт | CFG0612-FX-R010ELF (ERJ8BWFR010V) | 50 | https://www.elitan.ru/price/item20976639 | https://www.chipdip.ru/product0/8003933031
С58 | 8x11,5мм P:3.5мм, Конденсатор электролитический алюминиевый | ECAP (К50-35), 1000мкФ, 10В | 20 | https://www.chipdip.ru/product0/9000565921?from=suggest_product
DA4 | Понижающий DC-DC преобразователь, Uвх=до 40В, Uвых=1.23…37, 3А, 150кГц [TO-263-5L] | LM2596R-ADJ | 15 | https://www.chipdip.ru/product/lm2596r-adj
 | Крепеж радиатора к плате | Винт М2х6 круг , пл, шлиц - | 60 | https://mirekom.ru/price/product-5410.11
 | Крепеж микросхемы к радиатору | Винт М3х8, круг , пл, шлиц - | 20 | https://mirekom.ru/price/product-9764.14

Sheet: Константная часть
Позиция | Комментарий | Наименование | Кол-во | Link2URL | Link3URL | Link4URL | Link5URL
ANT1 | LTE Cellular Ceramic Antenna 698MHz-2.7GHz , SMT | 146200-00011 | 1 | https://www.elitan.ru/price/item17428368
Конденсаторы
C1, C11, C12, C13, C24, C28 | 4.7uF | GRM188R60J475KE19D | 6 | https://www.chipdip.ru/product/grm188r60j475ke19d | https://www.electronshik.ru/item/MUR/GRM188R60J475KE19D
C2, C3, C8, C14, C15, C16, C32, C34, C35, C40, C45, C46, C47, C48, C49, C52, C53, C54, C59, C61, C67, C68, C71, C76, C77, C79, C82 | 0.1uF | GRM188R71H104KA93D | 35 | https://www.chipdip.ru/product0/226236018 | https://www.electronshik.ru/item/MUR/GRM188R71H104KA93D
C4, C6, C17, C18, C29 | 10pF | GRM1885C1H100J | 5 | https://www.chipdip.ru/product/grm1885c1h100j | https://www.electronshik.ru/item/MUR/GRM1885C1H100JA01D
C5, C7, C9, C50, C51 | 22pF | GRM1885C1H220JA01D | 5 | https://www.chipdip.ru/product/grm1885c1h220j | https://www.electronshik.ru/item/MUR/GRM1885C1H220JA01D
C10 | 10nF | GRM188R71H103K | 1 | https://www.chipdip.ru/product0/9000143994 | https://www.electronshik.ru/item/MUR/GRM188R71H103KA01D
C19, C20, C44 | 33pF | GRM1885C1H330J | 3 | https://www.chipdip.ru/product0/565764982 | https://www.electronshik.ru/item/MUR/GRM1885C1H330JA01D
C21 | 100pF | GRM1885C1H101J | 1 | https://www.chipdip.ru/product0/305749128 | https://www.electronshik.ru/item/MUR/GRM1885C1H101JA01D
C22, C23, C25, C63 | 1uF | GRM188R71E105KA12D | 4 | https://www.chipdip.ru/product/grm188r71e105ka12d | https://www.electronshik.ru/item/MUR/GRM188R71E105KA12D
C26, C27 | 470uF 6.3V тип Е Конденсатор танталовый SMD | 293D477X06R3E2TE3 | 2 | https://www.chipdip.ru/product0/145634327?from=suggest_product
C30 | 1uF | GRM31MR71E105KA01L | 1 | https://www.chipdip.ru/product/grm31mr71e105k | https://www.electronshik.ru/item/MUR/GRM31MR71E105KA01L
C31 | 10uF 10V тип B Конденсатор танталовый SMD 10uF 10V | TECAP10/10VB10 | 1 | https://www.chipdip.ru/product0/146061461?from=suggest_product
C33, C80, C81 | 0.1uF | CL05B104KO5NNNC (CC0402KRX7R7BB104) | 3 | https://www.chipdip.ru/product1/8001849671?from=suggest_product | https://www.electronshik.ru/item/SAMSUNG/CL05B104KO5NNNC
C36 | 0.039uF | CC0603KRX7R9BB393 | 1 | https://www.chipdip.ru/product0/8160066189?from=suggest_product | https://www.elitan.ru/price/item8778633 | https://www.electronshik.ru/item/YAG/CC0603KRX7R9BB393
C37 | K50-35 470uF 16V 8х12мм Р:3.5мм Конденсатор электролитический алюминиевый | JRB1C471M03500800120000B | 1 | https://www.chipdip.ru/product0/9000565914
C38, C39 | K50-35 1000uF 25V 10x21мм Конденсатор электролитический алюминиевый | JRC1E102M05001000210000B | 2 | https://www.chipdip.ru/product0/9000565765?from=suggest_product
C41 | 22pF | GRM21A5C2E220J (CC0805JRNPO9BN220) | 1 | https://www.chipdip.ru/product0/29844 | https://www.electronshik.ru/item/MUR/GRM21A5C2E220JW01D
C55 | 100pF 2kV | C1206C101KGRACAUTO (CC1206JKNPODBN101) | 1 | https://www.elitan.ru/price/item16896874 | https://www.electronshik.ru/item/KEM/C1206C101KGRACAUTO
C56 | K50-35 220uF 50V 10x12мм Конденсатор электролитический алюминиевый | SH050M0220B5S-1012 | 1 | https://www.chipdip.ru/product0/9000565903
C57, C64 | 10uF | GRM188R61E106M | 2 | https://www.chipdip.ru/product/grm188r61e106m | https://www.electronshik.ru/item/MUR/GRM188R61E106MA73D
C60, C69, C74, C75 | K50-35 220uF 6.3V 5x11мм Р:2,5мм Конденсатор электролитический алюминиевый | ECA0JHG221 | 4 | https://www.chipdip.ru/product0/9000261774?from=suggest_product
C62 | K50-35 100uF 16V 5x11мм Конденсатор электролитический алюминиевый | SH016M0100A2F-0511 | 1 | https://www.chipdip.ru/product0/9000565888
C65, C78 | K50-35(мини) 33uF 6.3V 4х7мм Конденсатор электролитический алюминиевый | JRK0J330M01500400070000B | 2 | https://www.chipdip.ru/product0/9000261769
C66 | 0.47uF | C1608X7R1H474K080AC (CC0603KRX7R9BB474) | 1 | https://www.chipdip.ru/product0/8576565346 | https://www.electronshik.ru/item/TDK/C1608X7R1H474K080AC
C70 | K50-35 680uF 25V 10х16мм Р:5мм Конденсатор электролитический алюминиевый 680мкФ, 25В, | JRB1E681M05001000160000B | 1 | https://www.chipdip.ru/product0/9000565919
C72, C73 | K50-35 100uF 10V 5x11мм Конденсатор электролитический алюминиевый | SH010M0100B2F-0511 | 2 | https://www.chipdip.ru/product0/46079?from=suggest_product | https://www.chipdip.ru/product0/9000565886
Микросхемы
D1 | Multi-Band LTE-TDD/LTE-FDD/HSPA+ and GSM/GPRS/EDGE module | SIM7600E-H | 1 | http://www.mt-system.ru/SIMCom/SIM7600E-H
D2 | AUDIO CODEC MONO 20QFN | NAU8810YG | 1 | https://upverter.com/upn/revision/eec1ccdac07fe113/ | http://www.nuvoton.com/hq/resource-download.jsp?tp_GUID=DA00-NAU8810.1 | https://www.elitan.ru/price/index.php?find=NAU8810YG&delay=-1&mfg=all&seenform=y
D3 | Voltage Level Translator Bidirectional 1 Circuit 2 Channel 100Mbps 8-VSSOP | TXB0102DCU | 1 | https://www.elitan.ru/price/item692394 | https://www.chipdip.ru/product0/8002872138?from=suggest_product | https://www.electronshik.ru/item/TI/TXB0102DCUR
D4 | 4-Bit Bidirectional Voltage-Level Shifter with Auto Direction Sensing and +/-15 kV ESD Protect 14-TSSOP -40 to 85 | TXB0104PWR | 1 | https://www.elitan.ru/price/item703962
D6 | 4.50 V 150 ms Microcontroller Supervisory Circuit - SOT-23-3 | MCP130T-450I/TT | 1 | https://www.elitan.ru/price/item505438 | https://www.electronshik.ru/item/MCRCH/MCP130T-450I%3A%3ATT
D7 | PLL Clock Multiplier Single 8-Pin SOIC 3 V ~ 5.25 V | NB3N501DG | 1 | https://www.elitan.ru/price/item9787428 | https://www.electronshik.ru/item/ONS/NB3N501DG
D8 | 8-bit I/O expander for I2C bus with interrupt PCF8574(A)T/3 - 100kHz version PCA8574(A)D - 400kHz version | PCF8574AT | 1 | https://www.elitan.ru/price/item981552 | https://www.electronshik.ru/item/NXP/PCF8574AT%3A%3A3.518
DA1 | Amplifier IC 1-Channel _Mono_ Class AB 5-PENTAWATT 10W | TDA2003V | 1 | https://www.elitan.ru/price/item123031 | https://www.chipdip.ru/product/tda2003v?from=suggest_product | https://www.chipdip.ru/product/hs-117-30
DA2 | Импульсный понижающий регулятор напряжения, 5В, 3А, [TO-263] | LM2576S-5.0 | 1 | https://www.chipdip.ru/product/lm2576sx-5.0-nopb | https://www.elitan.ru/price/item100181
DA3 | Li-lon Battery Charger 1A Standalone Linear with Thermal Regulation in SOP-8 | TP4056 | 1 | https://www.elitan.ru/price/item26170288 | https://www.electronshik.ru/item/YOUTAI/TP4056
DA5 | 3A Fast Response LDO Regulator Operating Input Voltage Range: 3V to 16V 1.24V to 15V Adjustable Output Voltage | MIC29302WU | 1 | https://www.elitan.ru/price/item637427 | https://www.chipdip.ru/product0/8000649332 | https://www.electronshik.ru/item/MCRCH/MIC29302WU
DA6 | LDO +1.25...13.8 В, 1А [SOT-223] Линейный регулятор с низким падением напряжения, Максимальное входное напряжение, 20 В | LM1117GS-ADJ | 1 | https://www.chipdip.ru/product/lm1117gs-adj | https://www.elitan.ru/price/item21580115
DA7 | LDO +3.3 В, 1А [SOT-223] Линейный регулятор с низким падением напряжения, Максимальное входное напряжение, 20 В | LM1117GS-3.3 | 1 | https://www.chipdip.ru/product/lm1117gs-3.3 | https://www.elitan.ru/price/item21580113
DD1 | Analog - STM32L071C8T6 Микроконтроллер 32-Бит, Cortex-M3, 32МГц, 128КБ Flash, LCD, USB, ADC, DAC [LQFP-48] | STM32L151CBT6A | 1 | https://www.elitan.ru/price/item11268663 | https://www.chipdip.ru/product/stm32l151cbt6a-2
Предохранители
F1 | Самовосстанавливающийся предохранитель PTC 1.8A(hold) 3.6A(trip) 33VDC 40A 1.9W 5s 0.04Ohm SMD 3425 Solder Pad 9.5 X 6.71 X 3mm | MF-SM185/33-2 | 1 | https://www.elitan.ru/price/item781521 | https://www.chipdip.ru/product0/8001787493?from=suggest_product
F2 | Предохранитель SMD 6 VDC 2.5 A | 1812L125/6PR | 1 | https://www.elitan.ru/price/item387111 | https://www.electronshik.ru/item/LTL/1812L125%3A%3A6PR
Светодиоды
HL1 | TO-1608BC-MYF Vf =2 V, 20mA, 0603 | HL-PST-1608S31YC | 1 | https://www.chipdip.ru/product/to-1608bc-myf?from=suggest_product | https://www.chipdip.ru/product/gnl-3012ed
HL2 | TO-1608BC-MRE Vf =2 V, 20mA, 0603 | HL-PST-1608S9AC | 1 | https://www.chipdip.ru/product/to-1608bc-mre?from=suggest_product | https://www.elitan.ru/price/item16986056 | https://www.chipdip.ru/product/gnl-3012ed
HL3 | TO-1608BC-PG Vf =3.3 V, 20mA, 0603 | HL-PST-1608U51GC | 1 | https://www.chipdip.ru/product/to-1608bc-pg?from=suggest_product | https://www.elitan.ru/price/item16986058
HL4 | TO-1608BC-BF Vf =3.3 V, 20mA, 0603 | HL-PST-1608H203BC | 1 | https://www.chipdip.ru/product/to-1608bc-bf?from=suggest_product | https://www.elitan.ru/price/item16986057
Индуктивности
IND1 | 0805, Дроссель подавления ЭМП 120Ohm 25% 100MHz 3A | BLM21PG121SN1D | 1 | https://www.chipdip.ru/product0/8228217893 | https://www.elitan.ru/price/item1364359
IND2, IND3, IND4, IND8, IND9 | 0805, Дроссель подавления ЭМП 1KOhm 25% 100MHz 1.6A 0.12Ohm | BLM21SP102SN1D | 5 | https://www.chipdip.ru/product/blm21sp102sn1d | https://www.elitan.ru/price/item21298136
IND5, IND7 | 0805, Дроссель подавления ЭМП 220Ohm +25% 100MHz 2A 45mOhm | BLM21PG221SN1D | 2 | https://www.chipdip.ru/product/blm21pg221sn1d | https://www.elitan.ru/price/item305175
IND6 | 0805, Дроссель подавления ЭМП 100МГц:30Ом; 3А | BLM21PG300SN1D | 1 | https://www.chipdip.ru/product/blm21pg300sn1d | https://www.elitan.ru/price/item310735
L1 | Чип индуктивность многослойная неэкранированная 47нГн 5% 100МГц Maximum DC Current 300 mA Maximum DC Resistance 700 mOhms | LQG18HN47NJ | 1 | https://www.elitan.ru/price/item307313 | https://www.chipdip.ru/product/lqg18hn47nj?from=suggest_product
L2 | SMD индуктивность проволочная, на ферритовом сердечнике, экранированная 33uH 15% 1KHz 23Q-Factor Ferrite 2.8A 62mOhm | SRR1208-330YL | 1 | https://www.chipdip.ru/product/srr1208-330yl?from=suggest_product | https://www.elitan.ru/price/item319349
L3 | SMD индуктивность проволочная, на ферритовом сердечнике, экранированная 68uH 15% 1KHz 23Q-Factor Ferrite 2.8A 62mOhm | SRR1208-680YL | 1 | https://www.chipdip.ru/product1/8002012849?from=suggest_product | https://www.elitan.ru/price/item782382
LC1 | EMI фильтр индуктивно-емкостной 10A 150VDC 40дБ | BNX003-01 | 1 | https://www.elitan.ru/price/item279156 | https://www.chipdip.ru/product/bnx003-01?from=suggest_product
Резисторы
R1, R2, R9, R11, R13, R25, R78 | 0 | RC0603JR-070RL | 7 | https://www.chipdip.ru/product0/9000070541 | https://www.electronshik.ru/item/YAG/RC0603JR-070RL
R3, R73 | 68 | RC0603FR-0768RL | 2 | https://www.chipdip.ru/product0/9000079612 | https://www.electronshik.ru/item/YAG/RC0603FR-0768RL
R4, R5, R6, R27, R28, R31, R34, R35, R36, R38, R46, R47, R48, R49, R74, R75, R79, R80, R81, R82 | 10k | RC0603FR-0710KL (CRCW060310K0FKEA) | 20 | https://www.chipdip.ru/product0/9000079736 | https://www.electronshik.ru/item/VISHAY/CRCW060310K0FKEA
R14, R15, R16 | 22 | RC0603FR-0722RL (RC0603JR-0722RL) | 3 | https://www.chipdip.ru/product0/9000079564 | https://www.electronshik.ru/item/FENGHUA/0603%20-22%20%D0%9E%D0%BC%205%25%20RC0603JR-0722RL%20%5BRS-03K220JT%5D
R17, R20, R21, R26, R29, R39 | 2.2k | RC0603FR-072K2L | 6 | https://www.chipdip.ru/product0/9000079720 | https://www.electronshik.ru/item/YAG/RC0603FR-072K2L
R18, R19, R55, R64, R67 | 1k | RC0603FR-071KL | 5 | https://www.chipdip.ru/product0/9000079676 | https://www.electronshik.ru/item/YAG/RC0603FR-071KL
R30, R40 | 360 | RC0603FR-07360RL | 2 | https://www.chipdip.ru/product0/9000079629 | https://www.electronshik.ru/item/YAG/RC0603FR-07360RL
R33 | 22k | RC0603FR-0722KL | 1 | https://www.chipdip.ru/product0/9000079744 | https://www.electronshik.ru/item/YAG/RC0603FR-0722KL
R37 | 39 | RC0603FR-0739RL | 1 | https://www.chipdip.ru/product0/9000079606 | https://www.electronshik.ru/item/YAG/RC0603FR-0739RL
R41 | 43 | RC0603FR-0743RL | 1 | https://www.chipdip.ru/product0/9000079607 | https://www.electronshik.ru/item/YAG/RC0603FR-0743RL
R42 | 2.2 | RC0603FR-072R2L | 1 | https://www.chipdip.ru/product0/9000079549 | https://www.electronshik.ru/item/YAG/RC0603FR-072R2L
R43 | 1 | RC0603FR-071RL | 1 | https://www.chipdip.ru/product0/9000079509 | https://www.electronshik.ru/item/YAG/RC0603FR-071RL
R44, R68 | 0 | RC0805JR-070RL | 2 | https://www.chipdip.ru/product0/153356071 | https://www.electronshik.ru/item/YAG/RC0805JR-070RL
R45 | 10 | RC0603FR-0710RL | 1 | https://www.chipdip.ru/product0/9000079557 | https://www.electronshik.ru/item/YAG/RC0603FR-0710RL
R50 | 1M | RC1206JR-071ML | 1 | https://www.chipdip.ru/product0/690816980 | https://www.electronshik.ru/item/YAG/RC1206JR-071ML
R51 | 18k | RC0603FR-0718KL | 1 | https://www.chipdip.ru/product0/9000079742 | https://www.electronshik.ru/item/YAG/RC0603FR-0718KL
R52 | 3.9k | RC0603FR-073K9L | 1 | https://www.chipdip.ru/product0/9000079726?from=suggest_product | https://www.electronshik.ru/item/YAG/RC0603FR-073K9L
R53 | 2 SMD чип резистор, с проволочной обмоткой, 4527, 2 Ом, Серия WSC, 2 Вт | WSC45272R000FEA | 1 | https://www.chipdip.ru/product/wsc45272r000fea?from=suggest_product | https://www.elitan.ru/price/item572273
R56 | 100 | RC0603FR-07100RL | 1 | https://www.chipdip.ru/product0/9000079616 | https://www.electronshik.ru/item/YAG/RC0603FR-07100RL
R57 | 16k | RC0603FR-0716KL | 1 | https://www.chipdip.ru/product0/9000079741 | https://www.electronshik.ru/item/YAG/RC0603FR-0716KL
R58 | 1.5k | RC0603FR-071K5L | 1 | https://www.chipdip.ru/product0/9000079716?from=suggest_product | https://www.electronshik.ru/item/YAG/RC0603FR-071K5L
R59, R63 | 100k | RC0603FR-07100KL | 2 | https://www.chipdip.ru/product0/9000079760 | https://www.electronshik.ru/item/YAG/RC0603FR-07100KL
R60 | 47k | RC0603FR-0747KL | 1 | https://www.chipdip.ru/product0/9000079752 | https://www.electronshik.ru/item/YAG/RC0603FR-0747KL
R61 | 470 | RC0805FR-07470RL | 1 | https://www.chipdip.ru/product0/9000079478 | https://www.electronshik.ru/item/YAG/RC0805FR-07470RL
R62 | 10k | RC0603FR-0710KL (CRCW060310K0FKEA) | 1 | https://www.electronshik.ru/item/VISHAY/CRCW060310K0FKEA | https://www.chipdip.ru/product0/9000079736
R65 | 1.3k | RC0603FR-071K3L | 1 | https://www.chipdip.ru/product0/9000079679 | https://www.electronshik.ru/item/YAG/RC0603FR-071K3L
R66 | 0.1 | RL0805FR-070R1L | 1 | https://www.elitan.ru/price/item503786 | https://www.electronshik.ru/item/YAG/RL0805FR-070R1L
R69 | 3.3k | RC0603FR-073K3L | 1 | https://www.chipdip.ru/product0/9000079724 | https://www.electronshik.ru/item/YAG/RC0603FR-073K3L
R70 | 7.5k | RC0603FR-077K5L | 1 | https://www.chipdip.ru/product0/9000079733 | https://www.electronshik.ru/item/YAG/RC0603FR-077K5L
R71 | 1k | RC0402FR-071KL | 1 | https://www.chipdip.ru/product0/9000189652?from=suggest_product | https://www.electronshik.ru/item/YAG/RC0402FR-071KL
R72 | 1k | RC1206FR-071KL | 1 | https://www.chipdip.ru/product0/9000079635 | https://www.electronshik.ru/item/YAG/RC1206FR-071KL
R76, R84, R54 | 2k | RC0603FR-072KL | 3 | https://www.chipdip.ru/product0/9000079719 | https://www.electronshik.ru/item/YAG/RC0603FR-072KL
R83 | 5.6k | RC0603FR-075K6L | 1 | https://www.chipdip.ru/product1/8001784532 | https://www.electronshik.ru/item/YAG/RC0603FR-075K6L
Переключатели
S1, S2, S3, S5 | 6x6 Tact Switch Series | KLS7-TS6606 | 4 | https://www.chipdip.ru/product/kls7-ts6606-7.0-180-tc-0206 | https://www.elitan.ru/price/item22675038
S4 | SMD button | 1437566-3 | 1 | https://www.chipdip.ru/product/tyco-1437566-3-fsmsm?from=suggest_product | https://www.elitan.ru/price/item565583
Диоды, транзисторы
VD1 | 12.5V Clamp 8A _8/20µs_ Ipp Tvs Diode Surface Mount SC-88/SC70-6/SOT-363 | SMF05C | 1 | https://www.elitan.ru/price/item10155001 | https://www.chipdip.ru/product/smf05ct1g?from=suggest_product
VD2, VD3, VD4 | TVS диод защитный 5В_пиковое_рабочее 9.8В_ограничение SOD923 | ESD9L5.0ST5G | 3 | https://www.elitan.ru/price/index.php?find=ESD9L5.0ST5G&delay=-1&mfg=all&seenform=y | https://www.chipdip.ru/product0/8001926257
VD5, VD18 | Сборка защитная TVS-диодов 5.25В_пиковое_ SOT23-5 Unidirectional Channels 4 Voltage - Reverse Standoff (Typ) 5.25V Voltage - Breakdown (Min) 6.1V | ESDA6V1SC5 | 2 | https://www.elitan.ru/price/item317230 | https://www.electronshik.ru/item/ST/ESDA6V1SC5 | https://www.chipdip.ru/product0/8001797118?from=suggest_product
VD6 | TVS Diode-3 Рабочее напряжение 5.5 В Максимальное напряжение фиксации 8.5 в | SP0503BAHTG | 1 | https://www.chipdip.ru/product/sp0503bahtg | https://www.elitan.ru/price/item393293
VD7 | Стабилитрон 5.1В, 5%, 0.5Вт, [SOD-123] | MMSZ5231B-TP | 1 | https://www.chipdip.ru/product/mmsz5231b-tp?from=suggest_product | https://www.elitan.ru/price/item685173
VD8, VD9, VD17 | TVS диод защитный 5В_пиковое_рабочее 9.8В_ограничение SOD923 | ESD9L3.3ST5G | 3 | https://www.elitan.ru/price/item1205491 | https://www.chipdip.ru/product1/8002974897?from=suggest_product
VD10 | TVS диоды Подавители ЭСР / диоды для подавления переходных скачков напряжения ESD Protection Device | LXES15AAA1-153 | 1 | https://www.chipdip.ru/product0/8001818635?from=suggest_product | https://www.elitan.ru/price/item11962267
VD11, VD16 | Schottky; DO-214AB; 3.0A IF; 0.75V; 60V; 100A IFRM; 10000V/us; 1000pF | SS36 | 2 | https://www.elitan.ru/price/item499214 | https://www.chipdip.ru/product/ss36-e3-57t-2?from=suggest_product
VD14 | Schottky; DO-214AB; 3.0A IF; 0.75V; 40V; 100A IFRM; 10000V/us; 1000pF | BAT60AE6327HTSA1 | 1 | https://www.chipdip.ru/product/bat60a?from=suggest_product | https://www.elitan.ru/price/item9533309
VD15 | Transistor, Npn, 0.1A, 50V, Vbe = 0.7V, hfe = 240 [ SOT23 ] | SS34 | 1 | https://www.chipdip.ru/product/ss34-5 | https://www.elitan.ru/price/item9505516
VT1 | N-Channel MOSFET 60В 0.115А [SOT-23] | 2N7002 | 1 | https://www.chipdip.ru/product/2n7002-tp-reel-3000 | https://www.elitan.ru/price/item484309
VT2, VT3 | Диод Шоттки 3А 10В [SOD-323] | BC850B | 2 | https://www.chipdip.ru/product/bc850b?from=suggest_product | https://www.elitan.ru/price/item5642305
VT6, VT7 | P-Channel 20V 3.7A _Ta_ 1.3W _Ta_ Surface Mount/SOT-23 | IRLML6402 | 2 | https://www.chipdip.ru/product/irlml6402tr?from=suggest_product | https://www.elitan.ru/price/item13518502
VT5, VT8, VT9, VT10 | MOSFET, N-канал, 0.2А, 50В, [SOT-23] | BSS138 | 4 | https://www.chipdip.ru/product/bss138-7-f-diodes?from=suggest_product | https://www.elitan.ru/price/item305174
VT11 | MOSFET, N-канал 60В 1.9А [SOT-23] | SI2308BDS-T1-GE3 | 1 | https://www.chipdip.ru/product/si2308bds-t1-ge3-vishay | https://www.electronshik.ru/item/VISHAY/SI2308BDS-T1-GE3 | https://www.elitan.ru/price/item668096
Разъемы
X1 | Соединители для карт памяти 1mm microSIM Push Push SMT | 5039600696 | 1 | https://www.elitan.ru/price/item12310026
X2 | Разъем: для карт памяти; SD Micro; push-push; SMT; позолота | 112J-TDAR-R | 1 | https://www.chipdip.ru/product0/8002703228 | https://www.elitan.ru/price/item10898530
X3 | USB - micro B USB 2.0 Receptacle Connector 5 Position Surface Mount, Right Angle; Through Hole | 1050170001 | 1 | https://www.elitan.ru/price/item5116026 | https://www.chipdip.ru/product/105017-0001-molex?position_type={position_type}|k50id|pla-293946777986|cid|11945324864|aid|488785225626|gid|115765259517&utm_campaign=G_tovarnieobjavlenija&utm_content=text1_ga&utm_term=
X4 | Гнездо моно 2.5мм | PY-401N | 1 | https://www.elitan.ru/price/index.php?find=PY-401N&delay=-1&mfg=all&seenform=y | https://www.chipdip.ru/product/py-401n
X5 | Аудио гнездо (М) 3.5мм | PY-601N | 1 | https://www.chipdip.ru/product/py-601n?from=suggest_product | https://www.elitan.ru/price/index.php?find=PY-601N&delay=-1&mfg=all&seenform=y
X6, X13 | Вилка штыревая 2.54мм 1x2 прямая PLS-2 | DS1021_1x2 | 2 | https://www.chipdip.ru/product/pls-2 | https://www.elitan.ru/price/item10669650
X7 | Вилка на плату прямая 14 конт. 2.54мм ответная часть: DS1016-14MA2BB или IDC-14F шлейф DS1057-14A282R-30.5 | DS1013-14M | 1 | https://www.elitan.ru/price/item21920938 | https://www.electronshik.ru/item/CONNFLY/DS1013-14MSIXA-B | https://www.chipdip.ru/product0/8160149550
X8, X15 | Клеммник разъемный угловой 2 конт., шаг 5.08 мм (KLS2-EDR-5.08-02P-4) 2EDGK-5.08-02P - ответная часть | 2EDGR-5.08-02P | 2 | https://www.chipdip.ru/product/kls2-edr-5.08-02p-4-2edgr-5.08-02p | https://www.elitan.ru/price/item21239767
X9 | Разъем РЧ / 50 Ом Коаксиальный, UFL Коаксиальный, Прямое Гнездо, Вертикальный Поверхностный Монтаж SMT | U_FL-R-SMT-1_10 | 1 | https://www.elitan.ru/price/item1203541 | https://www.chipdip.ru/product0/9000586248?from=suggest_product
X10 | Разъем угловой SMA гнездо на плату 50 Ом | KLS1-SMA002-B | 1 | https://www.platan.ru/cgi-bin/qwery.pl/id=356964102 | https://www.elitan.ru/price/item9893558
X11 | Вилка штыревая 2.54мм 2x3 прямая тип1 | DS1021-2*3SF11-B | 1 | https://www.chipdip.ru/product/pld-6 | https://www.electronshik.ru/item/CONNFLY/DS1021-2x3SF11-B
X12 | Вилка штыревая 2.54мм 2х8 прямая PLD-16 | DS1021_2x8 | 1 | https://www.chipdip.ru/product/pld-16 | https://www.elitan.ru/price/item14835380
X14 | 16340 2/3A Battery Holder | Keystone 1029 | 1 | https://www.elitan.ru/price/item468733
Резонаторы. Генераторы
Y1 | 8 MHz resonator | HC49SM-8MHz | 1 | https://www.chipdip.ru/product/8mhz-hc-49sm | https://www.elitan.ru/price/item2093968
Прочее
 | Аккумулятор 16340 EAGTAC 750mAh защищенный | 16340 EagTac 750mAh 4,5А защищенный | 1 | https://magzaryada.ru/akkumulyatory/14500-16340/eagletac-16340-rcr123 | https://www.lacrosse-nn.ru/%D0%B0%D0%BA%D0%BA%D1%83%D0%BC%D1%83%D0%BB%D1%8F%D1%82%D0%BE%D1%80%D1%8B-li-ion-14500-16340-rcr123/eagtac-16340-750mah-4-5a/
 | Радиатор 30х43х20 мм, 7.1 дюйм*градус/Вт | HS 117-30 | 1 | https://www.chipdip.ru/product/hs-117-30 | https://www.electronshik.ru/item/KLS/HS117-30
 | LCD Cyrillic дисплей 16X2 | WH1602B-YYK-CTK | 1 | https://www.electronshik.ru/item/WINSTAR/WH1602B-YYK-CTK%23
 | Крепеж радиатора к плате | Винт М2х6 круг , пл, шлиц - | 2 |  | https://www.sovelektron.com/vint-pf2-6/ | https://mirekom.ru/price/product-5410.11 | https://mirekom.ru/price/product-4708.10
 | Разъемный клеммный блок, ответная часть 2 контакта. Серия 2EDGK-5.08 | 2EDGK-5.08-02P-14 | 2 | https://mirekom.ru/price/product-6612.20 | https://www.elitan.ru/price/item130957 | https://www.chipdip.ru/product/kls2-edk-5.08-02p-4s-2esdv-02p?from=suggest_product
 | Розетка кабельная с 14-контактами 2.54мм | IDC-14F (DS1016-14MA2BB) | 1 | https://www.elitan.ru/price/item8570145 | https://www.electronshik.ru/item/CONNFLY/DS1016-14MA2BB
 | Плоский шлейф 14 жил 1.27мм | DS1057-14A282R-30.5 | 1 | https://www.electronshik.ru/item/CONNFLY/DS1057-14A282R-30.5 | https://www.chipdip.ru/product/ds1057-14-30
 | Термопаста | GD900 30g | 1шт. На весь проект | https://tgt-store.ru/272186/ | https://aliexpress.ru/item/33047821777.html
 | Крепеж микросхемы к радиатору | Винт М3х8, круг , пл, шлиц - | 1
