MikhailBerezhanov/MAMboard/pcb/v1.0/AutoinformerPCB.pdf

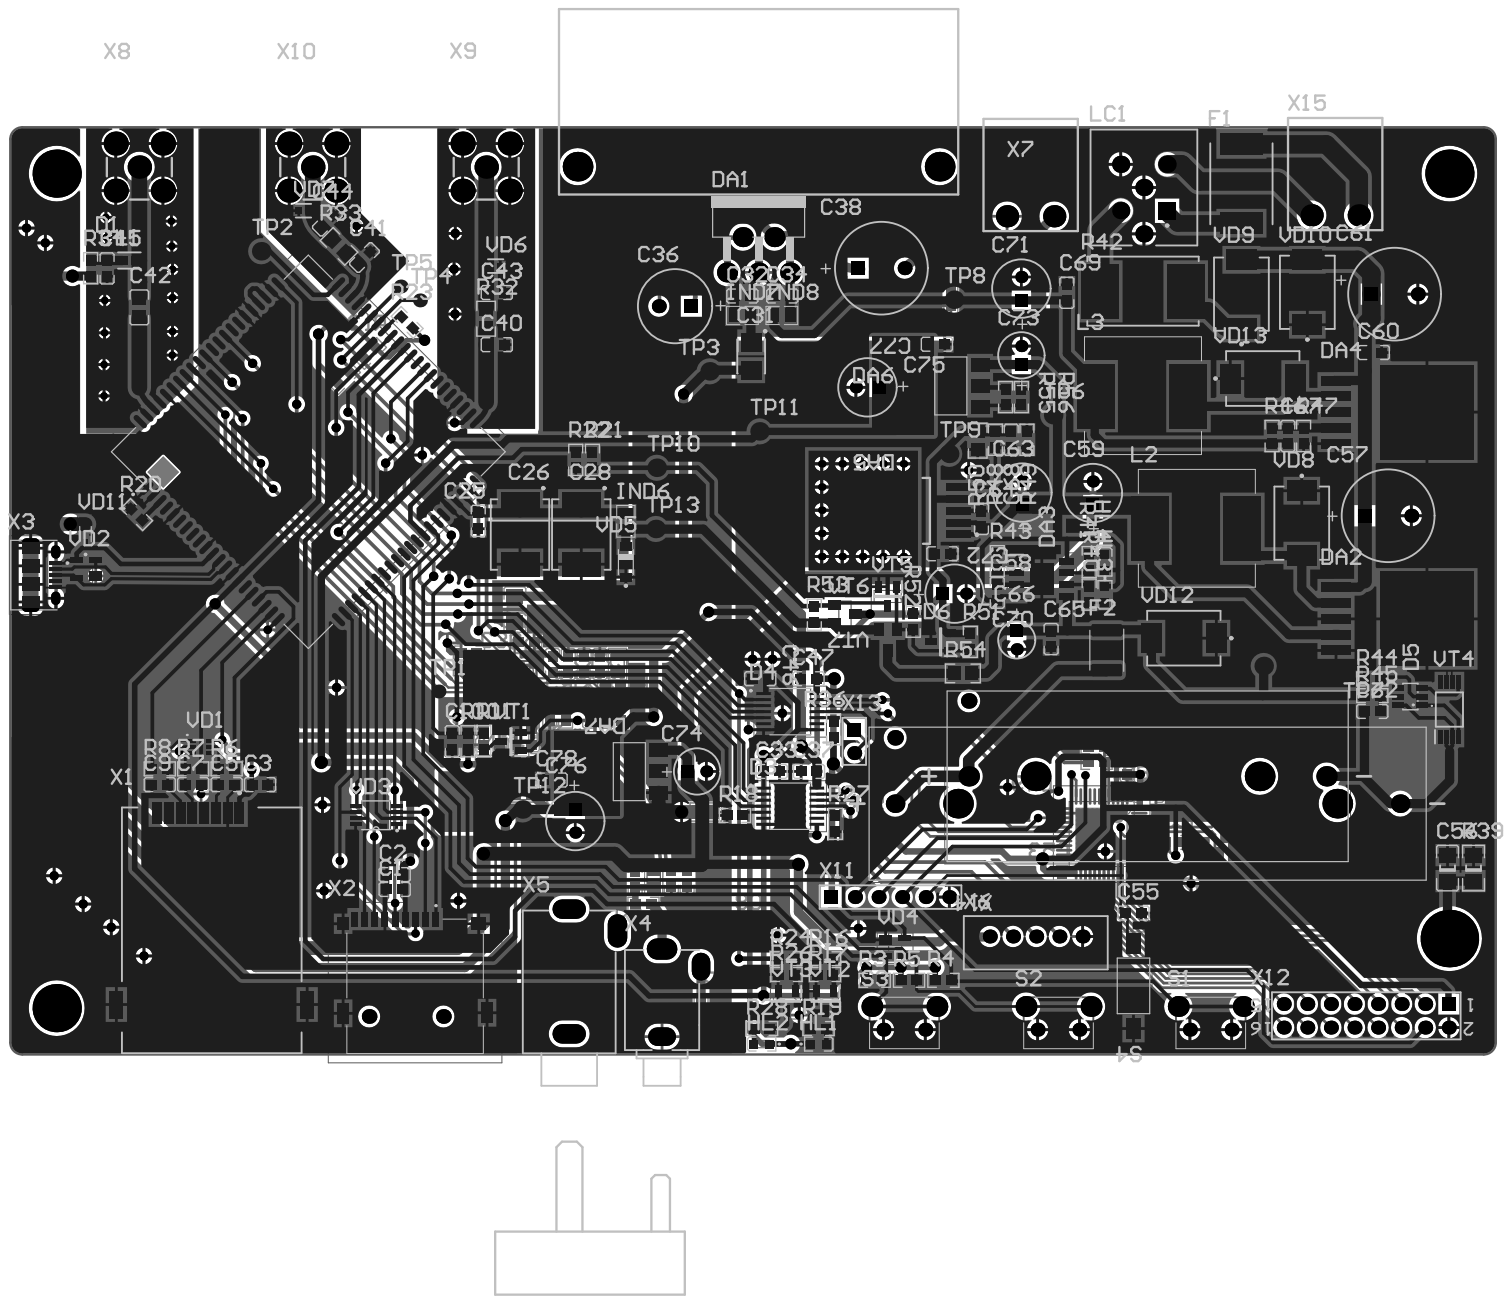
[picture p31: page 1]
