MikhailBerezhanov/MAMboard/pcb/v1.0/Project Outputs for Autoinformer/Autoinformer_v1.0_Assembly.pdf

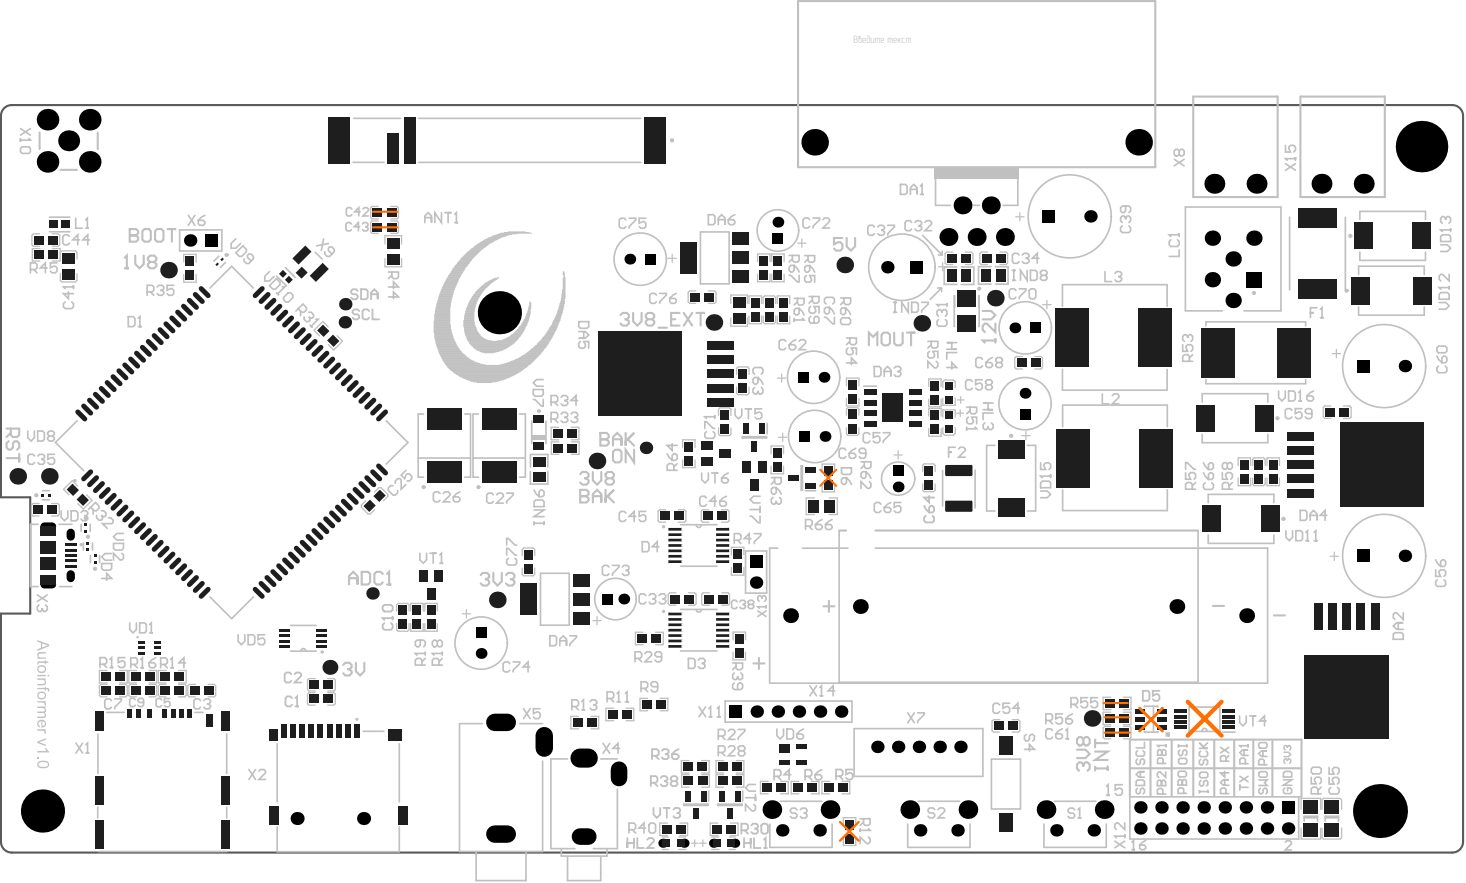
[picture p32: page 1]

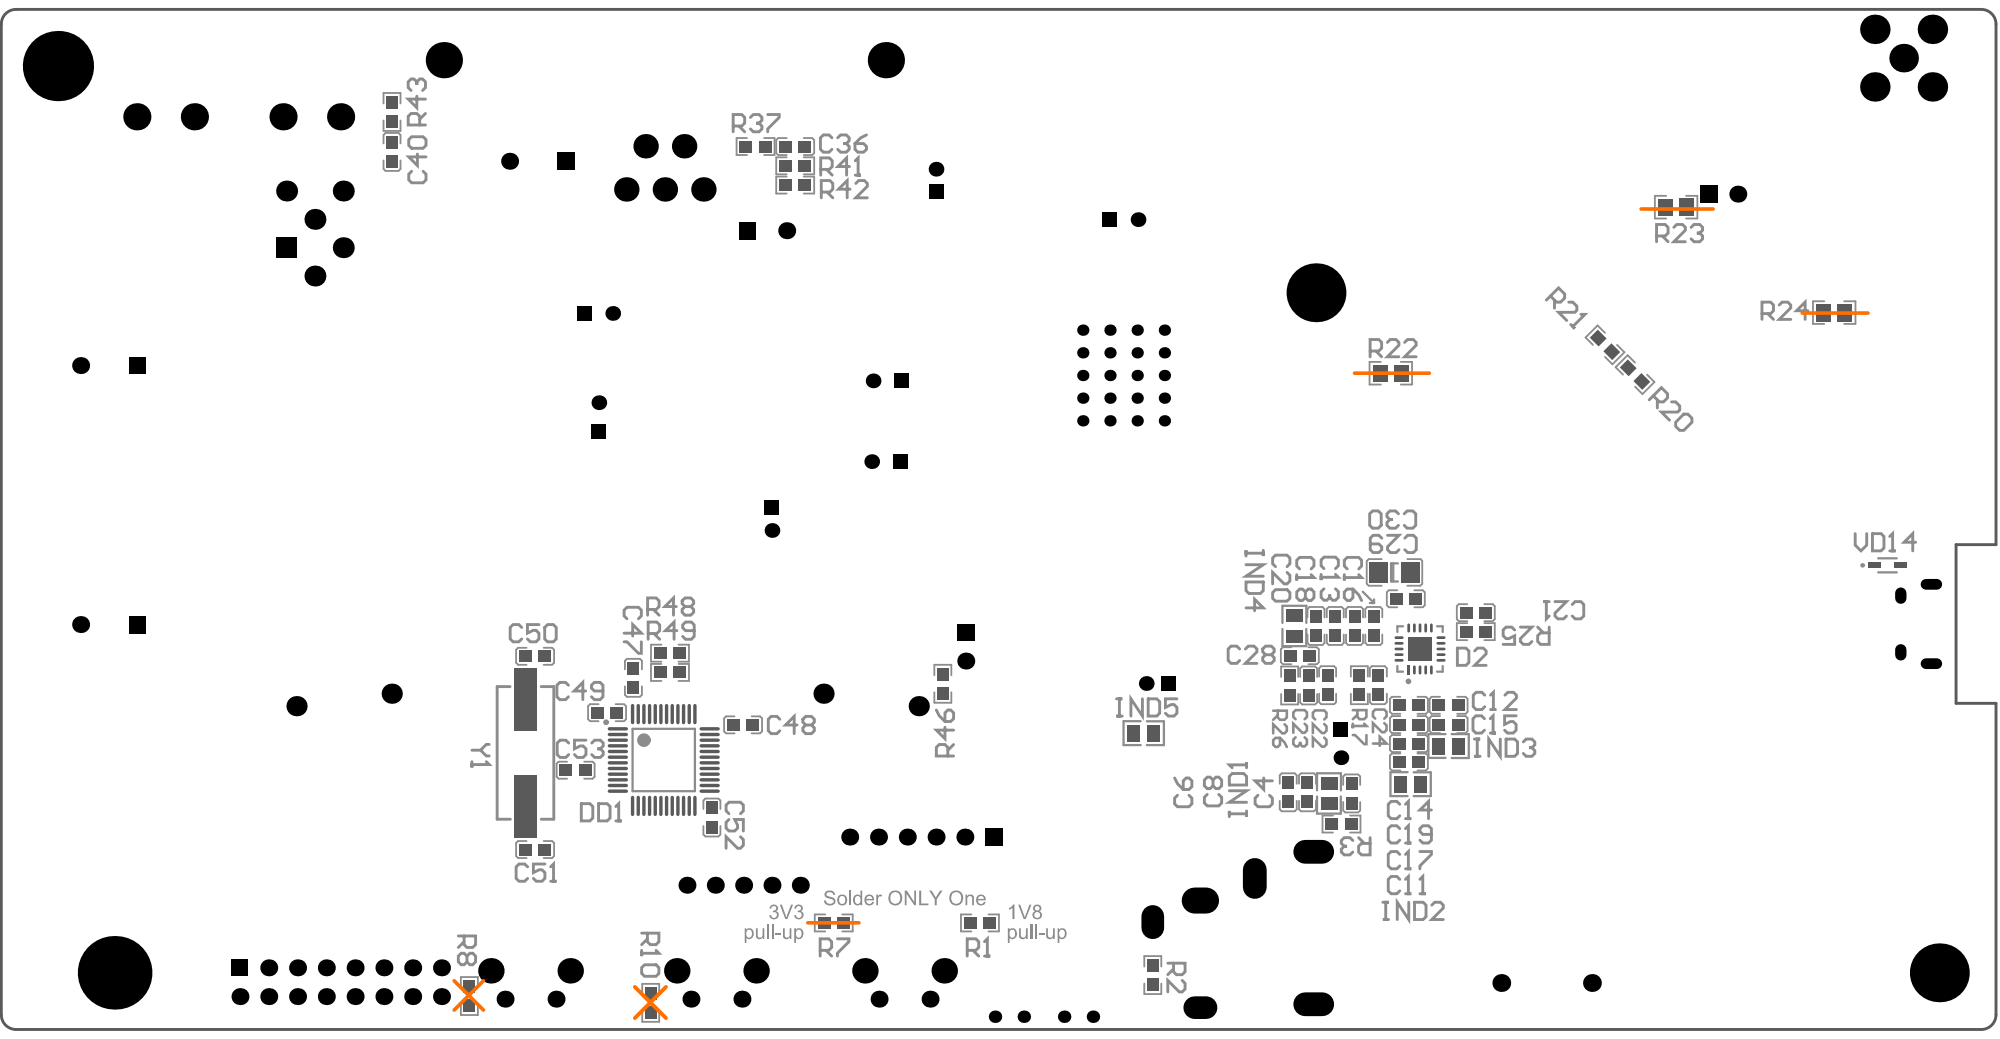
[picture p33: page 2]
