MikhailBerezhanov/MAMboard/pcb/v1.0/Project Outputs for Autoinformer/Autoinformer_v1.0_Assembly_Origin.PDF

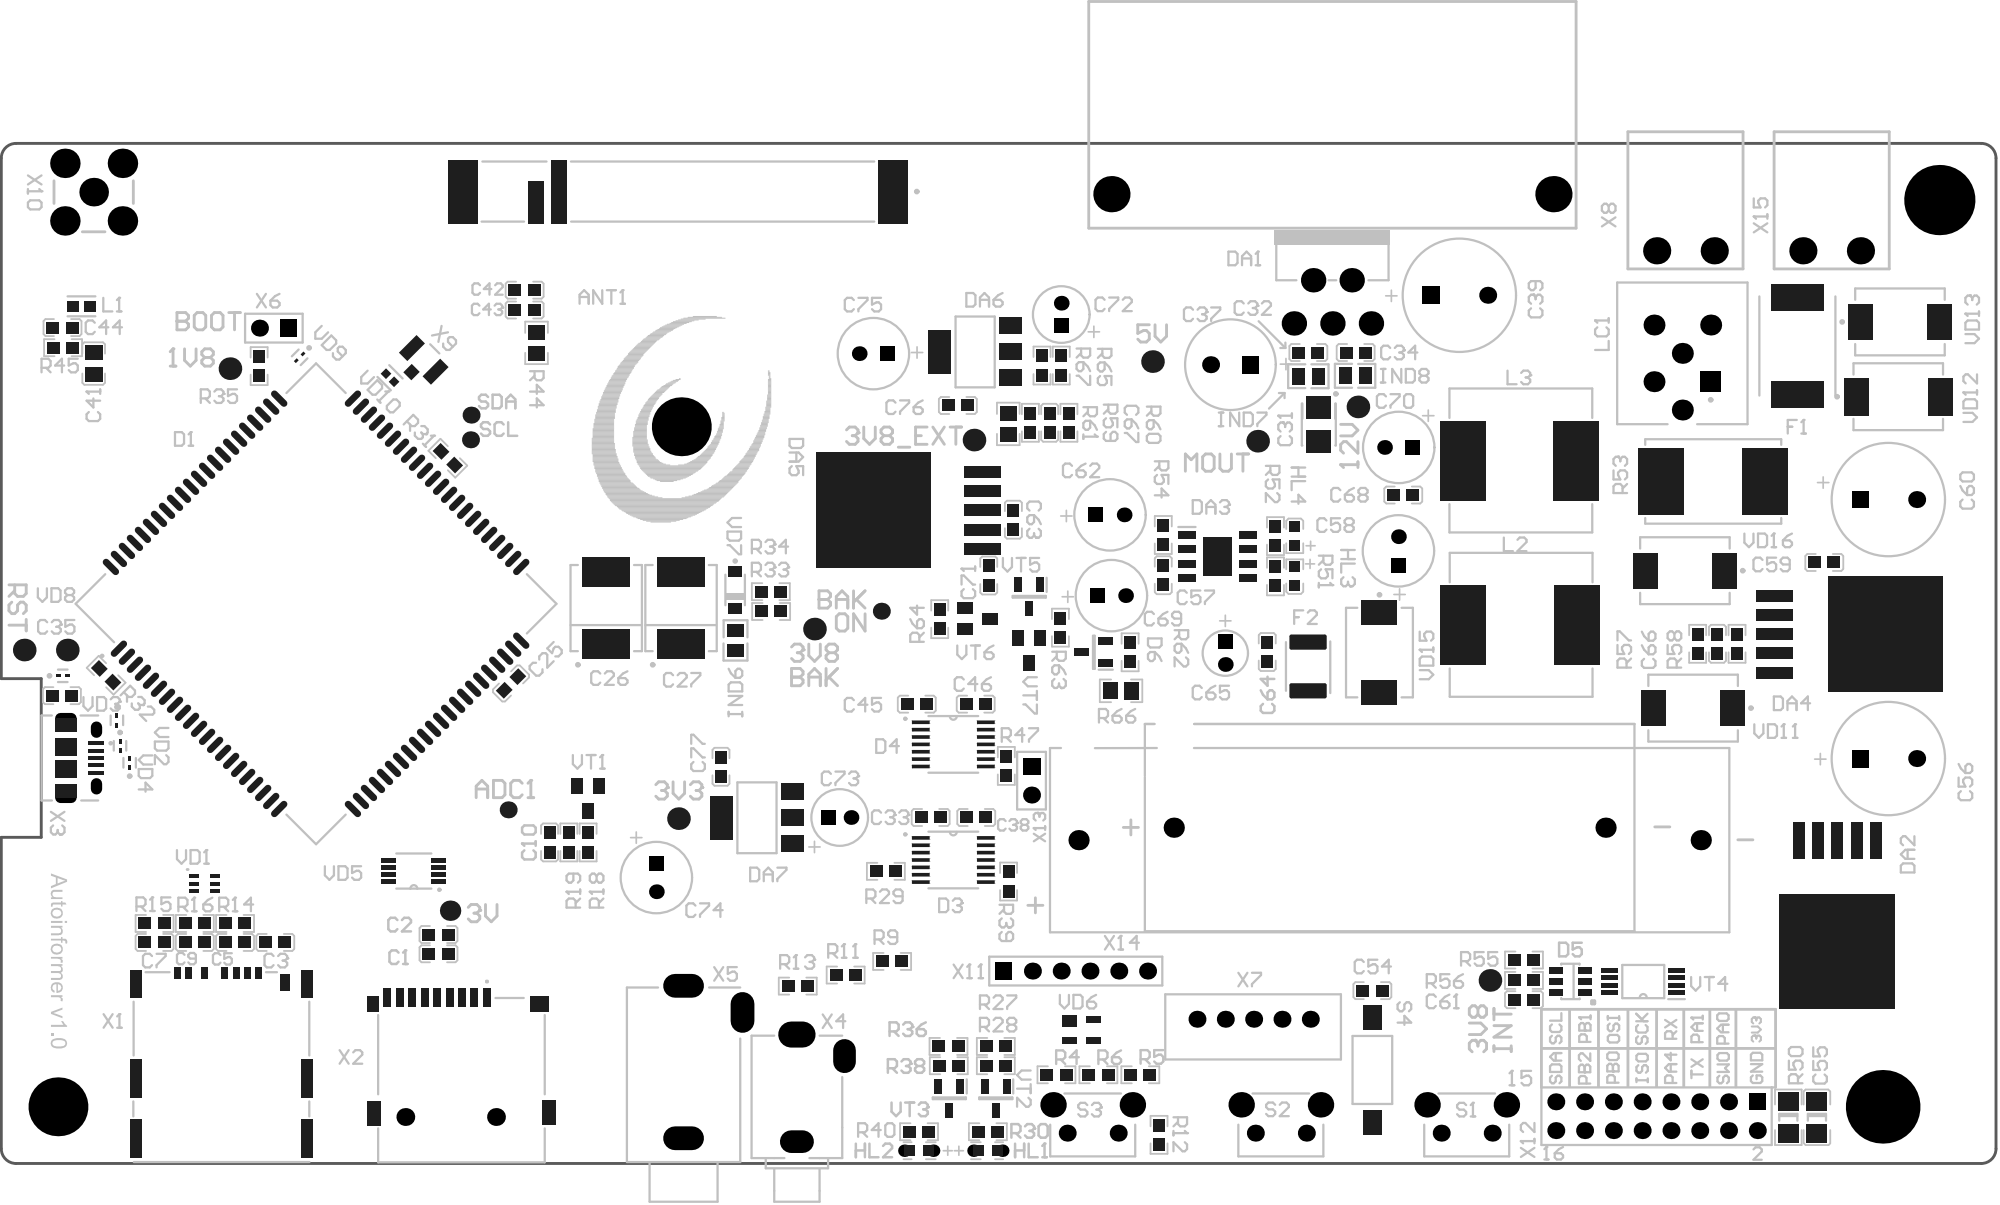
[picture p34: page 1]

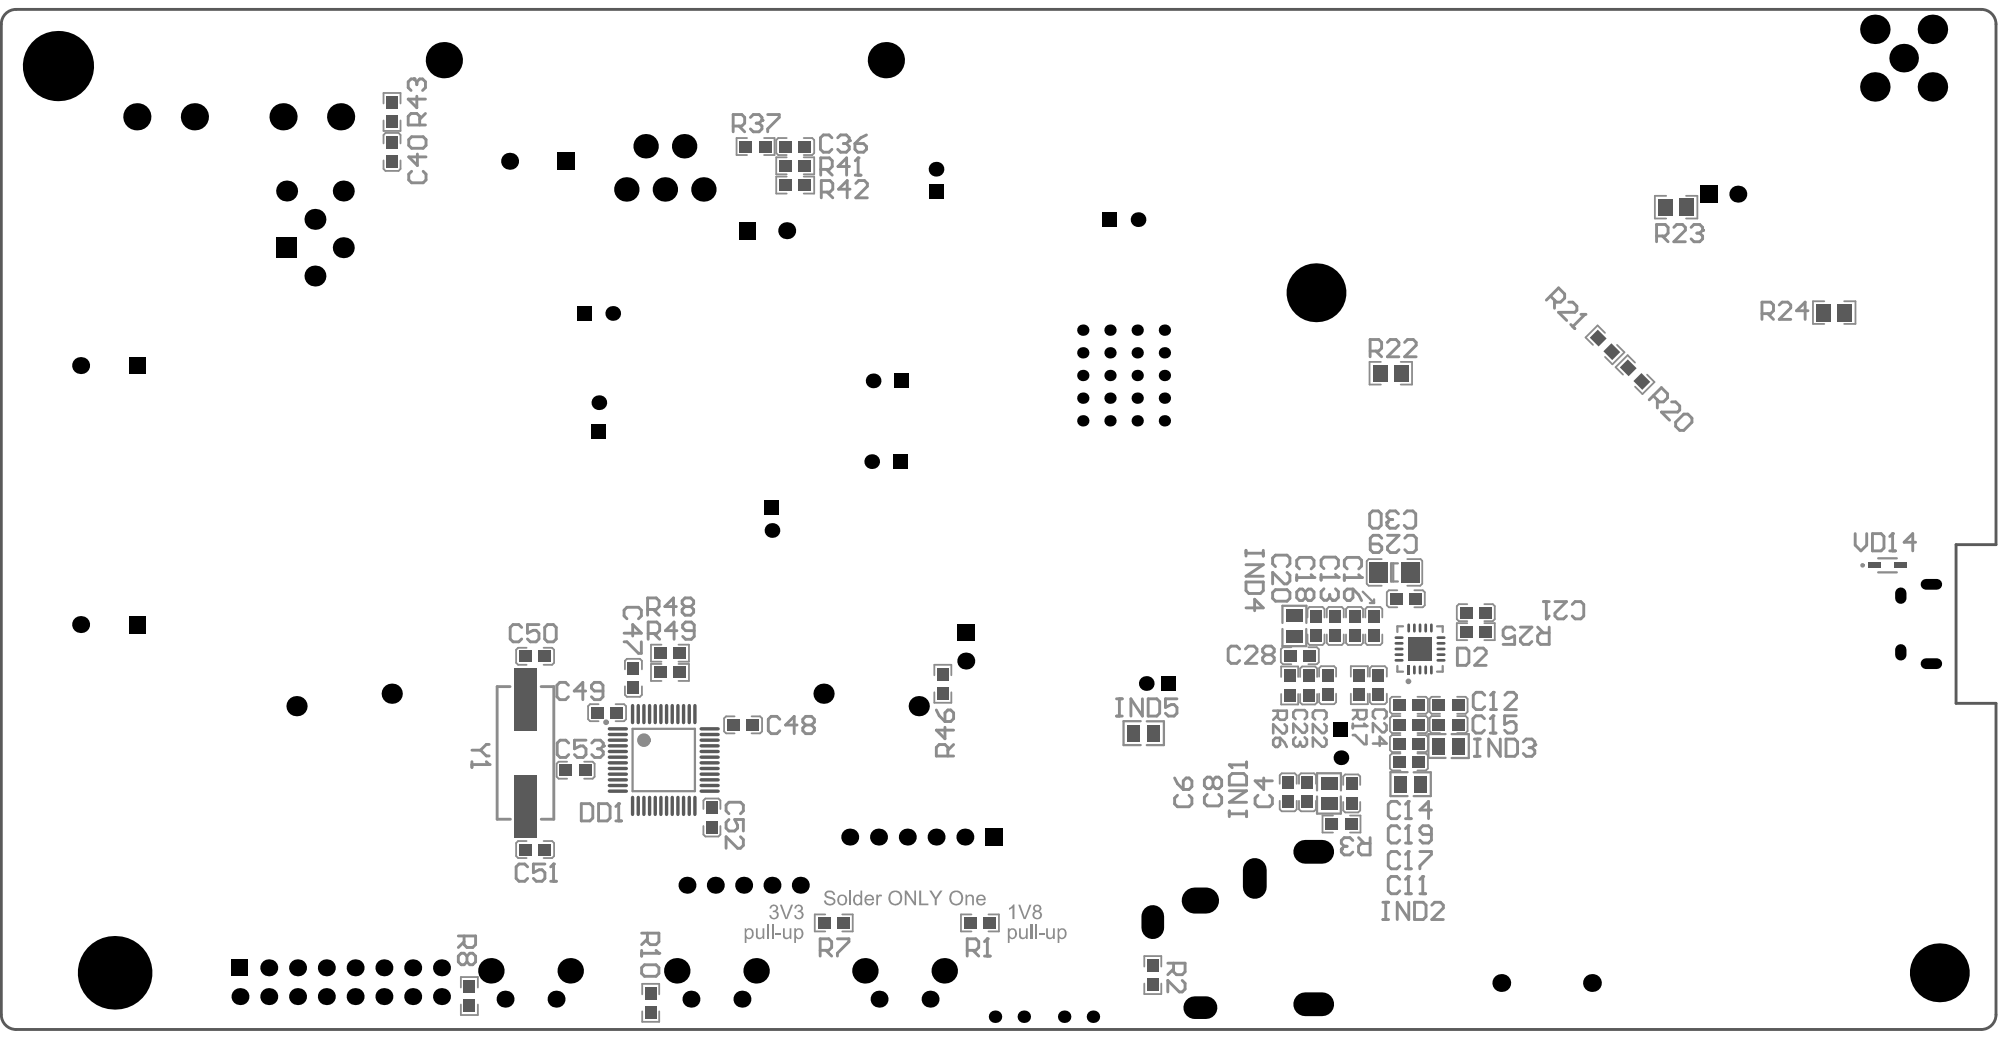
[picture p35: page 2]
